aronreid/ups-to-esp32/docs/ups-adaptor-onepager.pdf

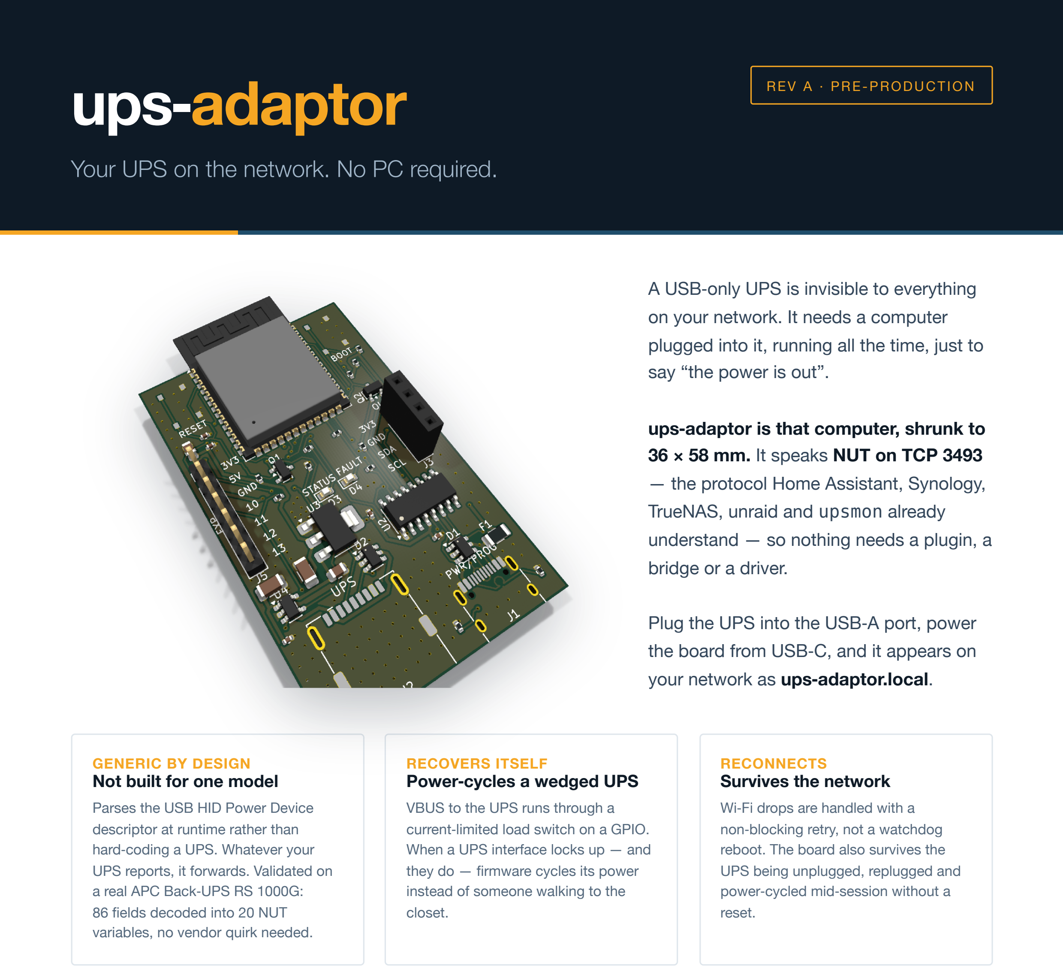
[picture p6: figure]
on your network. It needs a computer; say “the power is out”.; ups‑adaptor is that computer, shrunk to 36 × 58 mm. It speaks NUT on TCP 3493; TrueNAS, unraid and upsmon already; bridge or a driver.; Plug the UPS into the USB‑A port, power the board from USB‑C, and it appears on your network as ups‑adaptor.local.; GENERIC BY DESIGN Not built for one model; Parses the USB HID Power Device descriptor at runtime rather than hard‑coding a UPS. Whatever your UPS reports, it forwards. Validated on a real APC Back‑UPS RS 1000G: 86 fields decoded into 20 NUT variables, no vendor quirk needed.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

### A USB‑only UPS is invisible to everything

### plugged into it, running all the time, just to

— the protocol Home Assistant, Synology,

### understand — so nothing needs a plugin, a

## Technical specification

Controller | ESP32‑S3‑WROOM‑1‑N4 dual‑core Xtensa LX7, 4 MB flash
Wireless | Wi‑Fi 802.11 b/g/n, 2.4 GHz PCB antenna, Bluetooth disabled
UPS port | USB‑A host, USB 2.0 full speed 12 Mbps, HID Power Device class
VBUS to UPS | Switched, 1 A current limit fault flag to firmware, 100 µF bulk
Power & console | USB‑C: 5 V in, programming and serial on one connector
Protection | ESD array on both USB ports 2 A resettable polyfuse
Primary output | NUT server, TCP 3493 read‑only protocol subset
Secondary output | MQTT with Home Assistant discovery
Setup | Web UI over Wi‑Fi; SoftAP for first‑run provisioning
Discovery | mDNS — ups‑adaptor.local
Expansion | 4 × GPIO + 3V3 + 5V + GND I²C header for a 128×64 OLED
Board | 36 × 58 mm, 2 layer surface mount, case‑clip mounting

Open hardware & firmware. GPL‑3.0‑or‑later — KiCad sources, ESP‑IDF firmware and the test harness are all in the repository.

Rev A
Pre‑production. Not yet
fabricated.

Your UPS on the network. No PC required.
