aronreid/ups-to-esp32/firmware/components/ups_hid/ups_hid.c

/* SPDX-License-Identifier: GPL-3.0-or-later */
#include "ups_hid.h"
#include "hid_parser.h"
#include "tripplite_legacy.h"
#include "apc_modbus.h"
#include "status_hold.h"
#include "report_io.h"
#include "usb_guard.h"
#include "ups_vartab.h"
#include "ups_vars.h"
#include "ups_nutstatus.h"
#include "board.h"
#include "freertos/FreeRTOS.h"
#include "freertos/task.h"
#include "freertos/semphr.h"
#include "esp_log.h"
#include "esp_timer.h"
#include "esp_heap_caps.h"
#include "esp_attr.h"
#include "esp_system.h"
#include "usb/usb_host.h"
#include "usb/usb_helpers.h"
#include "mbedtls/sha256.h"
#include <math.h>
#include <string.h>

static const char *TAG = "ups_hid";

/* See usb_guard.h. RTC_NOINIT: survives the panic restart it exists to count. */
static RTC_NOINIT_ATTR usb_guard_state_t s_guard;
static usb_guard_level_t s_guard_level;
static int64_t s_live_until_us;

#define POLL_INTERVAL_MS      2000
#define FAILURES_BEFORE_RESET 5     /* ~10s of silence before a VBUS cycle */
/* After restoring VBUS, how long to wait for a bus-powered UPS to report that
 * it went away. A self-powered one never does; see do_recover(). */
#define VBUS_GONE_WAIT_MS     1500

/* How long to hold the last known status through an all-zero reading before
 * giving up and forcing a VBUS recovery. A CyberPower EC850LCD reported no
 * status bits for ~2 minutes after a test (2026-09-27, docs/rev-b.md); this
 * is comfortably longer than that observed glitch, short enough that a UPS
 * genuinely gone quiet still gets recovered well inside a shutdown script's
 * patience. */
#define STATUS_HOLD_US (5LL * 60 * 1000000)
_Static_assert(STATUS_HOLD_UNKNOWN == (uint32_t)UPS_STATUS_UNKNOWN,
               "status_hold.h's stand-in for UPS_STATUS_UNKNOWN drifted");

/* Recovery backoff. A UPS that is simply unplugged must not have its VBUS
 * cycled every ten seconds forever, but one that may yet come back must not be
 * abandoned either. Start at 10s and double to a 5 minute ceiling, reset on the
 * first good poll. */
#define RECOVERY_BACKOFF_MIN_US (10LL * 1000 * 1000)
#define RECOVERY_BACKOFF_MAX_US (300LL * 1000 * 1000)

static ups_data_t       s_data;
static hid_report_map_t s_map;
static SemaphoreHandle_t s_lock;

/* Kept outside ups_data_t because ups_hid_recover() resets that wholesale. */
static int64_t s_next_recovery_us;
static int64_t s_recovery_backoff_us = RECOVERY_BACKOFF_MIN_US;

/* A failed enumeration is tried again, on its own backoff. NEW_DEV fires once
 * per attach, so a UPS that fumbled its first descriptor read (a slow one, or
 * one still waking after a VBUS recovery) used to sit at "not detected" until
 * someone replugged it: the empty-port logic below kept the recovery idle,
 * because with nothing open there was nothing failing. */
#define ENUM_RETRY_MIN_US (2LL * 1000 * 1000)
#define ENUM_RETRY_MAX_US (60LL * 1000 * 1000)
static bool    s_enum_retry;            /* try s_dev_addr again at s_enum_retry_at_us */
static int64_t s_enum_retry_at_us;
static int64_t s_enum_backoff_us = ENUM_RETRY_MIN_US;
/* Enumeration failed and the device could not be closed (a control transfer
 * still parked): it counts as failing polls, so do_recover() takes over. */
static bool    s_enum_stuck;
/* The failure will not change on a retry: the address has gone, or the
 * device is not HID at all. */
static bool    s_enum_final;

static void ups_data_reset(ups_data_t *d)
{
    memset(d, 0, sizeof(*d));
    d->battery_charge    = UPS_VALUE_ABSENT;
    d->battery_runtime   = UPS_VALUE_ABSENT;
    d->battery_voltage   = UPS_VALUE_ABSENT;
    d->input_voltage     = UPS_VALUE_ABSENT;
    d->input_frequency   = UPS_VALUE_ABSENT;
    d->output_voltage    = UPS_VALUE_ABSENT;
    d->ups_load          = UPS_VALUE_ABSENT;
    d->ups_realpower     = UPS_VALUE_ABSENT;
    d->ups_realpower_nom = UPS_VALUE_ABSENT;
    d->ups_apparentpower = UPS_VALUE_ABSENT;
    d->status            = UPS_STATUS_UNKNOWN;
    d->battery_mfr_date[0] = '\0';
}

/* Values are read with GET_REPORT(Feature) on each poll. Feature, not Input:
 * a UPS keeps the authoritative reading there, and an Input report of the same
 * usage only arrives when the device chooses to send one.
 *           esp_hid's host component is input-report oriented and will not do
 *           this for us -- issue the control transfers directly (CLAUDE.md). */

/* ---- USB host plumbing ------------------------------------------------ */

#define USB_CLIENT_EVENT_TIMEOUT_MS 100
#define CTRL_TIMEOUT_MS             1000
/* NUT allows 6144. 2048 turned away real units: an Eaton (2053 bytes) and a
 * Legrand Keor DK 3K (2149) among the NUT issue captures, and three more sit
 * within 500 bytes of it. tools/test/test_nut_descriptors.py fails if any
 * capture outgrows this. */
#define REPORT_DESC_MAX             4096

#define USB_CLASS_HID               0x03
#define HID_DESC_TYPE               0x21
#define HID_REPORT_DESC_TYPE        0x22
#define REQ_GET_DESCRIPTOR          0x06
#define REQ_GET_REPORT              0x01
#define REQ_SET_REPORT              0x09
#define REPORT_TYPE_OUTPUT          0x02
#define REPORT_TYPE_FEATURE         0x03

static usb_host_client_handle_t s_client;
static usb_device_handle_t      s_dev;
static uint8_t                  s_dev_addr;
static bool                     s_dev_pending;
static uint8_t                  s_hid_iface = 0xFF;
static uint16_t                 s_report_desc_len;
static SemaphoreHandle_t        s_ctrl_done;
/* Legacy Tripp Lite (09ae:0001): a vendor protocol instead of HID Power
 * Device, answered on the interrupt IN endpoint. See tripplite_legacy.h. */
static bool                     s_legacy;
static uint8_t                  s_intr_ep;          /* 0 if the interface has none */
static uint16_t                 s_intr_mps;
static uint8_t                  s_intr_out_ep;      /* interrupt OUT, 0 if none */
/* APC Modbus over USB (apc_modbus.h): the descriptor carries the transport,
 * on these report IDs. The rest of its state is with NUT's variables. */
static bool                     s_mb;
static uint8_t                  s_mb_to, s_mb_from;
static SemaphoreHandle_t        s_intr_done;
static tl_config_t              s_tl;
static uint8_t                  s_report_desc[REPORT_DESC_MAX];

/* Worked out at enumeration; defined with the M1 polling code below. */
static void build_poll_plan(void);

/* The control table lives with the write path further down, but enumeration
 * and the poll plan both come first and need to see it. Kept in step with the
 * table by the static assert beside it. */
#define CTRL_COUNT 4
static const hid_field_t *s_ctrl_field[CTRL_COUNT];
static uint32_t discover_caps(void);

/* ManufacturerDate, Battery System 0x85. Neither a reading nor a control, so
 * it gets its own slot: read once per poll like everything else, but decoded
 * into text rather than a float. */
static const hid_field_t *s_date_field;

/* A command from another task, executed by the polling task. Declared here
 * because the poll loop and ups_hid_start are both above the definitions. */
typedef struct {
    ups_cmd_t cmd;
    int32_t   arg;
    /* Not a UPS command: a board-level VBUS power cycle, queued here so it
     * executes in ups_task like everything else that touches the report map. */
    bool      recover;
    /* Not a UPS command either: start (quiet_on) or end a quiet spell, see
     * ups_hid_quiet(). */
    bool      quiet;
    bool      quiet_on;
} cmd_req_t;
static QueueHandle_t s_cmd_q;
static QueueHandle_t s_cmd_done;
/* No USB traffic to the UPS: no interrupt pipe, no polls, no enumeration, no
 * commands. Set and cleared only in ups_task, by ups_hid_quiet(). */
static bool s_quiet;
static esp_err_t execute_cmd(const cmd_req_t *r);
static esp_err_t do_recover(void);
static void bind_vars(uint16_t vid, uint16_t pid);   /* NUT's tables, below */

static void ctrl_cb(usb_transfer_t *xfer)
{
    xSemaphoreGive((SemaphoreHandle_t)xfer->context);
}

/* A control transfer that timed out, still owned by the USB stack.
 *
 * THIS IS WHY BOARDS ON A CYBERPOWER CRASHED. ctrl_in and ctrl_out used to
 * free a transfer that had not completed in CTRL_TIMEOUT_MS -- while it was
 * still queued on the control pipe. The pipe's queue then pointed into freed
 * memory, the next allocation (a TLS handshake is the big one: an update
 * check) wrote over it, and when the stack next flushed the control pipe it
 * walked a corrupted list inside its critical section until the interrupt
 * watchdog reset the board. Recorded on a CyberPower EC850LCD, twice, v0.09:
 * hcd_pipe_command -> _pipe_cmd_flush -> _buffer_flush_all, from
 * usbh_process's handle_ep0_flush. An APC, which always answers in time,
 * never hit it.
 *
 * ESP-IDF has no public way to cancel a control transfer, and closing a
 * device with one in flight trips an assert. So a late one is PARKED: no new
 * control transfer is submitted until it completes -- when the UPS answers,
 * or the device goes away -- and only then is it freed. Only one control
 * transfer is ever in flight, so the shared completion semaphore stays
 * unambiguous. */
static usb_transfer_t *s_ctrl_parked;

/* Reclaim the parked transfer if it has completed, waiting up to wait_ms.
 * True when nothing is parked any more. */
static bool ctrl_reclaim(int wait_ms)
{
    if (!s_ctrl_parked) return true;
    for (int waited = 0; ; waited += 10) {
        if (xSemaphoreTake(s_ctrl_done, 0) == pdTRUE) {
            ESP_LOGW(TAG, "late control transfer completed (status %d); freed",
                     s_ctrl_parked->status);
            usb_host_transfer_free(s_ctrl_parked);
            s_ctrl_parked = NULL;
            return true;
        }
        if (waited >= wait_ms) return false;
        usb_host_client_handle_events(s_client, pdMS_TO_TICKS(10));
    }
}

/* Submit a control transfer and wait for it. False on refusal or timeout; a
 * timed-out transfer is parked, never freed -- see s_ctrl_parked. */
static bool ctrl_run(usb_transfer_t *xfer)
{
    xSemaphoreTake(s_ctrl_done, 0);         /* nothing else is in flight */
    if (usb_host_transfer_submit_control(s_client, xfer) != ESP_OK) return false;
    /* Transfer callbacks are delivered from usb_host_client_handle_events,
     * which this same task owns. Blocking on the semaphore without pumping
     * events deadlocks: the callback that would give it can never run. So
     * pump while waiting. */
    for (int waited = 0; waited < CTRL_TIMEOUT_MS; waited += 10) {
        usb_host_client_handle_events(s_client, pdMS_TO_TICKS(10));
        if (xSemaphoreTake(s_ctrl_done, 0) == pdTRUE) return true;
    }
    ESP_LOGW(TAG, "control transfer timed out; parked until the UPS answers");
    s_ctrl_parked = xfer;
    return false;
}

/* Close the device -- but never with a control transfer in flight, which
 * ESP-IDF asserts on. True if it was closed. */
static bool ipipe_stop(void);

static bool dev_close_safely(void)
{
    /* The standing interrupt transfer first: releasing the interface with it
     * still submitted is refused, and freeing it under the stack is how this
     * driver corrupted the heap once before. */
    if (!ipipe_stop()) {
        ESP_LOGE(TAG, "the interrupt transfer will not cancel; not closing the device yet");
        return false;
    }
    if (!ctrl_reclaim(1000)) {
        ESP_LOGE(TAG, "a control transfer is still in flight; not closing the device yet");
        return false;
    }
    usb_host_interface_release(s_client, s_dev, s_hid_iface);
    usb_host_device_close(s_client, s_dev);
    return true;
}

/* Blocking control OUT transfer: same shape as ctrl_in, with the payload
 * copied in after the setup packet instead of read out of it. Returns true if
 * the device ACKed. */
static bool ctrl_out(uint8_t bmRequestType, uint8_t bRequest, uint16_t wValue,
                     uint16_t wIndex, const uint8_t *data, uint16_t len)
{
    if (!ctrl_reclaim(2000)) return false;  /* the control pipe is still busy */
    usb_transfer_t *xfer = NULL;
    if (usb_host_transfer_alloc(sizeof(usb_setup_packet_t) + len, 0, &xfer) != ESP_OK) {
        return false;
    }

    usb_setup_packet_t *setup = (usb_setup_packet_t *)xfer->data_buffer;
    setup->bmRequestType = bmRequestType;
    setup->bRequest      = bRequest;
    setup->wValue        = wValue;
    setup->wIndex        = wIndex;
    setup->wLength       = len;
    if (len) memcpy(xfer->data_buffer + sizeof(usb_setup_packet_t), data, len);

    xfer->device_handle    = s_dev;
    xfer->bEndpointAddress = 0;
    xfer->num_bytes        = sizeof(usb_setup_packet_t) + len;
    xfer->callback         = ctrl_cb;
    xfer->context          = s_ctrl_done;

    if (!ctrl_run(xfer)) {
        if (xfer != s_ctrl_parked) usb_host_transfer_free(xfer);   /* refused */
        return false;
    }
    bool ok = xfer->status == USB_TRANSFER_STATUS_COMPLETED;
    usb_host_transfer_free(xfer);
    return ok;
}

/* Blocking control IN transfer. Returns bytes of payload, or -1. */
/* The attached device's EP0 max packet size, from its device descriptor. 64
 * until one is known: a multiple of every legal EP0 size, so rounding to it is
 * never too small. */
static uint8_t s_ep0_mps = 64;

/* The data stage of a control IN is sized in whole packets, not to wLength.
 * The host controller writes whatever packet the device sends, and some UPSes
 * answer a GET_REPORT with a full packet longer than the report asked for (an
 * APC Back-UPS ES 600M1 does, on its first feature poll). With the buffer cut
 * to exactly wLength, ESP-IDF's HCD does not fail the transfer: it asserts
 * (hcd_dwc.c, _buffer_parse_ctrl), and the board reboots and does it again on
 * every boot, off the network, until the UPS is unplugged. ESP-IDF documents
 * usb_round_up_to_mps() for exactly this; intr_in() already did it. */
static int ctrl_in(uint8_t bmRequestType, uint8_t bRequest, uint16_t wValue,
                   uint16_t wIndex, uint16_t wLength, uint8_t *out)
{
    if (!ctrl_reclaim(2000)) return -1;     /* the control pipe is still busy */
    size_t data = usb_round_up_to_mps(wLength, s_ep0_mps);
    usb_transfer_t *xfer = NULL;
    if (usb_host_transfer_alloc(sizeof(usb_setup_packet_t) + data, 0, &xfer) != ESP_OK) {
        return -1;
    }

    usb_setup_packet_t *setup = (usb_setup_packet_t *)xfer->data_buffer;
    setup->bmRequestType = bmRequestType;
    setup->bRequest      = bRequest;
    setup->wValue        = wValue;
    setup->wIndex        = wIndex;
    setup->wLength       = wLength;

    xfer->device_handle    = s_dev;
    xfer->bEndpointAddress = 0;
    xfer->num_bytes        = sizeof(usb_setup_packet_t) + data;
    xfer->callback         = ctrl_cb;
    xfer->context          = s_ctrl_done;

    int got = -1;
    if (!ctrl_run(xfer)) {
        if (xfer != s_ctrl_parked) usb_host_transfer_free(xfer);   /* refused */
        return -1;
    }
    if (xfer->status == USB_TRANSFER_STATUS_COMPLETED) {
        got = xfer->actual_num_bytes - sizeof(usb_setup_packet_t);
        if (got < 0) got = 0;
        if (got > wLength) got = wLength;
        if (out && got > 0) memcpy(out, xfer->data_buffer + sizeof(usb_setup_packet_t), got);
    }
    usb_host_transfer_free(xfer);
    return got;
}

/* Set by client_event_cb, acted on by ups_task at a point where no control
 * transfer is in flight. See the DEV_GONE case for why the teardown cannot
 * happen in the callback. */
static volatile bool s_dev_gone;

static void client_event_cb(const usb_host_client_event_msg_t *msg, void *arg)
{
    switch (msg->event) {
    case USB_HOST_CLIENT_EVENT_NEW_DEV:
        s_dev_addr = msg->new_dev.address;
        s_dev_pending = true;
        s_enum_retry = false;               /* a fresh attach starts afresh */
        s_enum_backoff_us = ENUM_RETRY_MIN_US;
        /* A crash from here until USB_GUARD_LIVE_US passes is charged to it. */
        s_guard.live = 1;
        s_live_until_us = esp_timer_get_time() + USB_GUARD_LIVE_US;
        ESP_LOGI(TAG, "USB device attached at address %u", s_dev_addr);
        break;
    case USB_HOST_CLIENT_EVENT_DEV_GONE:
        /* Heap is logged on every attach and detach so a leak across
         * plug cycles is VISIBLE. Repeated enumeration is where USB stacks
         * leak handles, and it will not show up as a failure for hundreds of
         * cycles -- by which time it is a field fault, not a bench one.
         * CLAUDE.md requires this board to survive replugging indefinitely. */
        ESP_LOGW(TAG, "USB device disconnected (heap %u free, %u low-water)",
                 (unsigned)esp_get_free_heap_size(),
                 (unsigned)esp_get_minimum_free_heap_size());
        /* FLAG ONLY. Do not release the interface or close the device here.
         *
         * This callback is dispatched by usb_host_client_handle_events(), and
         * ctrl_in()/ctrl_out() have to CALL that while waiting for a control
         * transfer to complete -- this task owns the event pump, so blocking
         * without pumping would deadlock. The consequence is that a device
         * disconnecting mid-poll runs this callback from INSIDE the transfer
         * wait, and the old code then released the interface and closed the
         * device handle while that transfer was still submitted against it,
         * after which ctrl_in() freed the transfer the stack still owned.
         *
         * Unplugging a UPS during a poll is not an exotic case; it is the
         * documented requirement in CLAUDE.md that this board survive being
         * unplugged mid-session. The attach path already had this right --
         * USB_HOST_CLIENT_EVENT_NEW_DEV only sets s_dev_pending and lets
         * ups_task open the device at a safe point. Detach now matches. */
        s_dev_gone = true;
        break;
    default:
        break;
    }
}

/* A UPS that has stopped answering must stop reporting numbers.
 *
 * An unplug clears everything through ups_data_reset(), but a UPS that is
 * still enumerated and has simply gone deaf -- the exact failure the VBUS
 * recovery exists for -- took a different path: `attached` went false and the
 * last good readings stayed behind it. The web UI then showed "UPS not
 * detected" next to a 100% battery and 120 V input, and NUT would have served
 * the same numbers to a client deciding whether to shut a NAS down.
 *
 * Identity is deliberately kept. Knowing WHICH UPS stopped answering is useful
 * and cannot be stale in any way that matters; a voltage can. */
static void invalidate_readings(ups_data_t *d)
{
    d->battery_charge    = UPS_VALUE_ABSENT;
    d->battery_runtime   = UPS_VALUE_ABSENT;
    d->battery_voltage   = UPS_VALUE_ABSENT;
    d->input_voltage     = UPS_VALUE_ABSENT;
    d->input_frequency   = UPS_VALUE_ABSENT;
    d->output_voltage    = UPS_VALUE_ABSENT;
    d->ups_load          = UPS_VALUE_ABSENT;
    d->ups_realpower     = UPS_VALUE_ABSENT;
    d->ups_realpower_nom = UPS_VALUE_ABSENT;
    d->ups_apparentpower = UPS_VALUE_ABSENT;
    d->status            = UPS_STATUS_UNKNOWN;
}

static void usb_lib_task(void *arg)
{
    for (;;) {
        uint32_t flags;
        usb_host_lib_handle_events(portMAX_DELAY, &flags);
        if (flags & USB_HOST_LIB_EVENT_FLAGS_NO_CLIENTS) {
            usb_host_device_free_all();
        }
    }
}

/* Walk the configuration descriptor for a HID interface and its report
 * descriptor length. Generic: matches on class, never on VID/PID. */
/* Every HID interface on the device, in order. A composite device can have
 * several, and the UPS is not always the first: a Liebert PSI5 (10af:0002)
 * puts a 27-byte vendor tunnel on interface 0 and the UPS on 1; NUT's Arduino
 * and Powervar subdrivers name interfaces 2 and 1. choose_hid_interface()
 * picks by content, not by a table of numbers. */
#define MAX_HID_IFACES 4
static struct { uint8_t iface; uint16_t desc_len; uint8_t ep; uint16_t mps; uint8_t ep_out; } s_hid_cand[MAX_HID_IFACES];
static size_t s_hid_cand_n;

static bool find_hid_interface(const usb_config_desc_t *cfg)
{
    int offset = 0;
    const usb_standard_desc_t *d = (const usb_standard_desc_t *)cfg;
    int cur = -1;                           /* index in s_hid_cand, or -1 */

    s_hid_cand_n = 0;
    while ((d = usb_parse_next_descriptor(d, cfg->wTotalLength, &offset)) != NULL) {
        if (d->bDescriptorType == USB_B_DESCRIPTOR_TYPE_INTERFACE) {
            const usb_intf_desc_t *i = (const usb_intf_desc_t *)d;
            cur = -1;
            if (i->bInterfaceClass == USB_CLASS_HID && i->bAlternateSetting == 0 &&
                s_hid_cand_n < MAX_HID_IFACES) {
                cur = (int)s_hid_cand_n;
                s_hid_cand[cur].iface = i->bInterfaceNumber;
                s_hid_cand[cur].desc_len = 0;
                s_hid_cand[cur].ep = 0;
                s_hid_cand[cur].mps = 0;
                s_hid_cand[cur].ep_out = 0;
            }
        } else if (cur >= 0 && d->bDescriptorType == HID_DESC_TYPE) {
            /* HID descriptor: wDescriptorLength is at offset 7. */
            const uint8_t *raw = (const uint8_t *)d;
            if (d->bLength >= 9 && !s_hid_cand[cur].desc_len) {
                s_hid_cand[cur].desc_len = (uint16_t)(raw[7] | (raw[8] << 8));
                if ((size_t)cur == s_hid_cand_n) s_hid_cand_n++;
            }
        } else if (cur >= 0 && d->bDescriptorType == USB_B_DESCRIPTOR_TYPE_ENDPOINT) {
            /* The endpoint descriptors follow the HID descriptor. The IN
             * endpoint carries the interrupt pipe and the legacy Tripp Lite
             * replies; the OUT one, APC Modbus requests (apc_modbus.h). */
            const usb_ep_desc_t *ep = (const usb_ep_desc_t *)d;
            if ((ep->bEndpointAddress & 0x80) && (ep->bmAttributes & 0x03) == 0x03 &&
                !s_hid_cand[cur].ep) {
                s_hid_cand[cur].ep = ep->bEndpointAddress;
                s_hid_cand[cur].mps = ep->wMaxPacketSize & 0x7FF;
            } else if (!(ep->bEndpointAddress & 0x80) && (ep->bmAttributes & 0x03) == 0x03 &&
                       !s_hid_cand[cur].ep_out) {
                s_hid_cand[cur].ep_out = ep->bEndpointAddress;
            }
        }
    }
    if (!s_hid_cand_n) return false;
    s_hid_iface = s_hid_cand[0].iface;      /* the default: the first */
    s_report_desc_len = s_hid_cand[0].desc_len;
    s_intr_ep = s_hid_cand[0].ep;
    s_intr_mps = s_hid_cand[0].mps;
    s_intr_out_ep = s_hid_cand[0].ep_out;
    return true;
}

static int ctrl_in(uint8_t bmRequestType, uint8_t bRequest, uint16_t wValue,
                   uint16_t wIndex, uint16_t wLength, uint8_t *out);

/* With more than one HID interface, the first whose report descriptor is a
 * UPS's (hid_is_power_device()). None is: keep the first, as before. */
static void choose_hid_interface(void)
{
    if (s_hid_cand_n < 2) return;
    for (size_t k = 0; k < s_hid_cand_n; k++) {
        uint16_t len = s_hid_cand[k].desc_len;
        if (!len || len > REPORT_DESC_MAX) continue;
        int n = ctrl_in(0x81, REQ_GET_DESCRIPTOR, (uint16_t)(HID_REPORT_DESC_TYPE << 8),
                        s_hid_cand[k].iface, len, s_report_desc);
        if (n > 0 && hid_is_power_device(s_report_desc, (size_t)n)) {
            s_hid_iface = s_hid_cand[k].iface;
            s_report_desc_len = s_hid_cand[k].desc_len;
            s_intr_ep = s_hid_cand[k].ep;
            s_intr_mps = s_hid_cand[k].mps;
            s_intr_out_ep = s_hid_cand[k].ep_out;
            ESP_LOGI(TAG, "%u HID interfaces; the UPS is interface %u",
                     (unsigned)s_hid_cand_n, s_hid_iface);
            return;
        }
    }
    ESP_LOGW(TAG, "%u HID interfaces, none a UPS descriptor; using interface %u",
             (unsigned)s_hid_cand_n, s_hid_iface);
}

/* Blocking interrupt IN read. Returns bytes read, or -1 on timeout or error.
 *
 * A timed-out transfer is still owned by the USB stack. It is CANCELLED --
 * halt, flush, clear -- and its completion awaited before it is freed; freeing
 * a transfer the stack still holds is how this driver once corrupted the heap
 * on unplug. */
static int intr_in(uint8_t *out, size_t cap, int timeout_ms)
{
    if (!s_intr_ep) return -1;
    size_t mps = s_intr_mps ? s_intr_mps : TL_PKT;
    /* Whole packets, and only as many as one TL_PKT reply needs. ESP-IDF ends
     * an interrupt IN transfer on a short packet or a full buffer, nothing
     * else: asking for 64 bytes on an 8-byte endpoint left every exact 8-byte
     * reply waiting for seven more, so each query timed out and the UPS was
     * never found. */
    size_t want = mps;
    while (want < TL_PKT) want += mps;
    if (want > cap) return -1;

    usb_transfer_t *xfer = NULL;
    if (usb_host_transfer_alloc(want, 0, &xfer) != ESP_OK) return -1;
    xfer->device_handle    = s_dev;
    xfer->bEndpointAddress = s_intr_ep;
    xfer->num_bytes        = want;
    xfer->callback         = ctrl_cb;
    xfer->context          = s_intr_done;
    xSemaphoreTake(s_intr_done, 0);         /* drop any stale completion */

    if (usb_host_transfer_submit(xfer) != ESP_OK) {
        usb_host_transfer_free(xfer);
        return -1;
    }
    bool done = false;
    for (int waited = 0; waited < timeout_ms; waited += 10) {
        usb_host_client_handle_events(s_client, pdMS_TO_TICKS(10));
        if (xSemaphoreTake(s_intr_done, 0) == pdTRUE) { done = true; break; }
    }
    if (!done) {
        usb_host_endpoint_halt(s_dev, s_intr_ep);
        usb_host_endpoint_flush(s_dev, s_intr_ep);
        for (int waited = 0; waited < 500 && !done; waited += 10) {
            usb_host_client_handle_events(s_client, pdMS_TO_TICKS(10));
            done = xSemaphoreTake(s_intr_done, 0) == pdTRUE;
        }
        usb_host_endpoint_clear(s_dev, s_intr_ep);
        if (!done) {
            /* Never completed even when cancelled: leak it rather than free
             * memory the stack may still write to. */
            ESP_LOGE(TAG, "interrupt transfer would not cancel; leaking %u bytes",
                     (unsigned)want);
            return -1;
        }
        usb_host_transfer_free(xfer);
        return -1;
    }
    int got = -1;
    if (xfer->status == USB_TRANSFER_STATUS_COMPLETED) {
        got = xfer->actual_num_bytes;
        if (got > (int)cap) got = (int)cap;
        memcpy(out, xfer->data_buffer, got);
    }
    usb_host_transfer_free(xfer);
    return got;
}

/* ---- The interrupt pipe ------------------------------------------------
 *
 * A UPS also sends Input reports on its interrupt endpoint when something
 * changes. NUT maps them by path onto the same variables and status tokens
 * as the polled Feature reports, so a change shows up before the next poll.
 * One transfer stands submitted; its callback only copies the bytes and sets
 * a flag, and ups_task does the rest and resubmits at a safe point. Stopping
 * it (dev_close_safely, every way a device is closed) cancels it, waits for
 * its completion, and only then frees it -- or refuses to close.
 *
 * Not used for the legacy Tripp Lite protocol (it talks on this endpoint
 * itself), nor while usb_guard.h has stopped polling. */
static usb_transfer_t  *s_ipipe;
static volatile bool    s_ipipe_busy, s_ipipe_ready;
static uint8_t          s_ipipe_buf[64];
static volatile int     s_ipipe_len;
static bool             s_ipipe_on;

static void ipipe_cb(usb_transfer_t *x)
{
    if (x->status == USB_TRANSFER_STATUS_COMPLETED && x->actual_num_bytes > 0) {
        int n = x->actual_num_bytes;
        if (n > (int)sizeof(s_ipipe_buf)) n = sizeof(s_ipipe_buf);
        memcpy(s_ipipe_buf, x->data_buffer, n);
        s_ipipe_len = n;
        s_ipipe_ready = true;
    }
    s_ipipe_busy = false;
}

static void ipipe_start(void)
{
    s_ipipe_on = false;
    if (!s_intr_ep || s_legacy || s_guard_level != USB_GUARD_NORMAL || s_ipipe || s_quiet) return;
    size_t mps = s_intr_mps ? s_intr_mps : 8;
    size_t want = mps;                      /* whole packets, at least 64 bytes */
    while (want < sizeof(s_ipipe_buf)) want += mps;
    if (usb_host_transfer_alloc(want, 0, &s_ipipe) != ESP_OK) { s_ipipe = NULL; return; }
    s_ipipe->device_handle    = s_dev;
    s_ipipe->bEndpointAddress = s_intr_ep;
    s_ipipe->num_bytes        = want;
    s_ipipe->callback         = ipipe_cb;
    s_ipipe->context          = NULL;
    s_ipipe_busy = s_ipipe_ready = false;
    s_ipipe_on = true;
    ESP_LOGI(TAG, "listening on interrupt endpoint 0x%02x", s_intr_ep);
}

static void ipipe_kick(void)
{
    if (!s_ipipe_on || s_ipipe_busy || s_dev_gone || !s_dev || s_quiet) return;
    s_ipipe_busy = true;
    if (usb_host_transfer_submit(s_ipipe) != ESP_OK) {
        s_ipipe_busy = false;
        s_ipipe_on = false;                 /* polling carries on regardless */
        ESP_LOGW(TAG, "interrupt endpoint refused a transfer; not listening");
    }
}

static bool ipipe_stop(void)
{
    s_ipipe_on = false;
    if (!s_ipipe) return true;
    if (s_ipipe_busy && s_dev) {
        usb_host_endpoint_halt(s_dev, s_intr_ep);
        usb_host_endpoint_flush(s_dev, s_intr_ep);
        for (int w = 0; w < 500 && s_ipipe_busy; w += 10) {
            usb_host_client_handle_events(s_client, pdMS_TO_TICKS(10));
        }
        usb_host_endpoint_clear(s_dev, s_intr_ep);
        if (s_ipipe_busy) return false;     /* still the stack's: do not free */
    }
    usb_host_transfer_free(s_ipipe);
    s_ipipe = NULL;
    s_ipipe_ready = false;
    return true;
}

/* Start or end a quiet spell. ups_task only: see ups_hid_quiet(). Quiet takes
 * effect at once for anything not yet sent; the interrupt pipe's standing
 * transfer is cancelled here, while nothing else is touching flash. */
static esp_err_t set_quiet(bool on)
{
    s_quiet = on;
    if (on) {
        ESP_LOGI(TAG, "quiet: UPS USB traffic paused");
        return ipipe_stop() ? ESP_OK : ESP_ERR_TIMEOUT;
    }
    ESP_LOGI(TAG, "quiet over: UPS USB traffic resumed");
    if (s_ipipe) s_ipipe_on = true;         /* a cancel that never came back */
    else if (s_dev && !s_dev_gone && s_guard_level == USB_GUARD_NORMAL) ipipe_start();
    return ESP_OK;
}

/* One legacy command and its reply. The UPS answers on the interrupt endpoint
 * a moment later, and echoes its PREVIOUS reply if it did not take this
 * command, so a reply counts only if it starts with this command's letter.
 *
 * Bounded well below NUT's loop, which can block for 100 s: this runs in
 * ups_task, and a stuck poll holds up the command queue and the recovery
 * logic behind it. Three sends, each read up to three times. */
static bool tl_xfer(const char *msg, size_t len, uint8_t reply[TL_PKT])
{
    uint8_t pkt[TL_PKT];
    tl_build_cmd((const uint8_t *)msg, len, pkt);
    for (int send = 0; send < 3; send++) {
        if (!ctrl_out(0x21, REQ_SET_REPORT, (uint16_t)(REPORT_TYPE_FEATURE << 8),
                      s_hid_iface, pkt, TL_PKT)) {
            continue;
        }
        vTaskDelay(pdMS_TO_TICKS(100));     /* NUT: replies take 80-90 ms */
        for (int rx = 0; rx < 3; rx++) {
            uint8_t buf[64];
            int n = intr_in(buf, sizeof(buf), 400);
            if (n >= TL_PKT && tl_reply_is_for(pkt, buf)) {
                memcpy(reply, buf, TL_PKT);
                return true;
            }
        }
    }
    return false;
}

/* Legacy enumeration: which protocol, watchdog off, configuration. */
static bool tl_enumerate(ups_data_t *local)
{
    if (!s_intr_ep) {
        ESP_LOGE(TAG, "legacy Tripp Lite without an interrupt IN endpoint");
        return false;
    }
    if (!s_intr_done) s_intr_done = xSemaphoreCreateBinary();
    if (!s_intr_done) return false;

    uint8_t r[TL_PKT];
    if (!tl_xfer("\0", 2, r)) {
        ESP_LOGE(TAG, "legacy Tripp Lite: no answer to the protocol query");
        return false;
    }
    uint16_t proto = tl_protocol_from_reply(r);
    tl_config_init(&s_tl, tl_decode_protocol(proto));
    ESP_LOGI(TAG, "legacy Tripp Lite, protocol %04x: %s", proto, tl_model_name(s_tl.model));

    /* The watchdog powers the load off if nothing talks to the UPS in time.
     * NUT turns it off on every model but SMARTPRO, which has none. */
    if (s_tl.model != TL_SMARTPRO && !tl_xfer("W\0", 3, r)) {
        ESP_LOGW(TAG, "legacy Tripp Lite: could not turn the watchdog off");
    }
    if (tl_xfer("V", 2, r)) tl_decode_v(&s_tl, r);
    ESP_LOGI(TAG, "legacy Tripp Lite: %d V input, %d V battery",
             s_tl.input_nominal, s_tl.battery_nominal);

    if (!local->mfr[0]) strlcpy(local->mfr, "Tripp Lite", sizeof(local->mfr));
    local->caps = 0;        /* no controls ported: tests and shutdown stay NUT-only */
    s_legacy = true;
    return true;
}

/* One legacy poll into d. False only when the UPS stops answering; an
 * unrecognised status code keeps the readings and reports the status as
 * unknown, rather than counting as a failure -- which would send a unit that
 * always says it into the VBUS recovery loop. */
static bool tl_poll(ups_data_t *d)
{
    char cmds[4];
    size_t n = tl_poll_commands(s_tl.model, cmds);
    tl_reading_t rd;
    tl_reading_init(&rd);
    for (size_t i = 0; i < n; i++) {
        char msg[2] = { cmds[i], 0 };
        uint8_t r[TL_PKT];
        if (!tl_xfer(msg, 2, r)) return false;
        switch (cmds[i]) {
        case 'S': tl_decode_s(&s_tl, r, &rd); break;
        case 'B': tl_decode_b(&s_tl, r, &rd); break;
        case 'D': tl_decode_d(&s_tl, r, &rd); break;
        case 'T': tl_decode_t(&s_tl, r, &rd); break;
        case 'L': tl_decode_l(&s_tl, r, &rd); break;
        default: break;
        }
    }
    tl_estimate_charge(&rd);

    uint32_t st = 0;
    if (rd.status & TL_ST_OL)   st |= UPS_STATUS_ONLINE;
    if (rd.status & TL_ST_OB)   st |= UPS_STATUS_ONBATT | UPS_STATUS_DISCHARGE;
    if (rd.status & TL_ST_LB)   st |= UPS_STATUS_LOWBATT;
    if (rd.status & TL_ST_RB)   st |= UPS_STATUS_REPLACEBATT;
    if (rd.status & TL_ST_OVER) st |= UPS_STATUS_OVERLOAD;
    d->status = rd.stale ? UPS_STATUS_UNKNOWN : st;

    d->battery_charge  = rd.battery_charge;
    d->battery_voltage = rd.battery_voltage;
    d->input_voltage   = rd.input_voltage;
    d->input_frequency = rd.input_frequency;
    d->output_voltage  = rd.output_voltage;
    d->ups_load        = rd.load;
    return true;
}

static void read_string(uint8_t index, char *out, size_t cap)
{
    out[0] = '\0';
    if (!index) return;
    uint8_t buf[128];
    /* 0x0409 = US English. */
    int n = ctrl_in(0x80, REQ_GET_DESCRIPTOR, (uint16_t)(0x0300 | index), 0x0409,
                    sizeof(buf), buf);
    if (n < 2) return;

    /* bLength is authoritative, NOT the transfer length. We asked for 128
     * bytes; what comes back past the descriptor's own length is padding or
     * whatever was in the buffer, and decoding it produced "EC850LCD???" from
     * a CyberPower EC850LCD -- three characters of junk that then travelled
     * out through NUT's ups.model to every client. */
    size_t len = buf[0];
    if (len > (size_t)n) len = (size_t)n;

    size_t o = 0;
    for (size_t i = 2; i + 1 < len && o + 1 < cap; i += 2) {
        uint16_t ch = buf[i] | (buf[i + 1] << 8);
        /* Anything outside printable ASCII is DROPPED rather than replaced
         * with '?'. These strings end up in ups.model and on the status page,
         * where a client shows them verbatim, so a shorter honest string beats
         * a padded one. Non-Latin names are the cost, and no UPS ships one. */
        if (ch >= 0x20 && ch < 0x7F) out[o++] = (char)ch;
    }
    out[o] = '\0';
    while (o && out[o - 1] == ' ') out[--o] = '\0';   /* APC pads with spaces */
}

/* Open the attached device, claim its HID interface, fetch and parse the
 * report descriptor. Returns true when the device is ready to poll. */
static bool enumerate(void)
{
    s_enum_final = false;
    esp_err_t oerr = usb_host_device_open(s_client, s_dev_addr, &s_dev);
    if (oerr != ESP_OK) {
        ESP_LOGE(TAG, "device_open failed: %s", esp_err_to_name(oerr));
        s_dev = NULL;
        s_enum_final = (oerr == ESP_ERR_NOT_FOUND);     /* it has gone */
        return false;
    }

    const usb_device_desc_t *dd = NULL;
    if (usb_host_get_device_descriptor(s_dev, &dd) != ESP_OK) {
        ESP_LOGE(TAG, "get_device_desc failed");
        return false;
    }
    s_ep0_mps = dd->bMaxPacketSize0 ? dd->bMaxPacketSize0 : 64;

    const usb_config_desc_t *cfg = NULL;
    if (usb_host_get_active_config_descriptor(s_dev, &cfg) != ESP_OK) {
        ESP_LOGE(TAG, "get_config_desc failed");
        return false;
    }

    if (!find_hid_interface(cfg)) {
        ESP_LOGE(TAG, "no HID interface on %04x:%04x -- not a HID Power Device?",
                 dd->idVendor, dd->idProduct);
        s_enum_final = true;
        return false;
    }

    choose_hid_interface();
    if (usb_host_interface_claim(s_client, s_dev, s_hid_iface, 0) != ESP_OK) {
        ESP_LOGE(TAG, "interface_claim(%u) failed", s_hid_iface);
        return false;
    }

    ups_data_t local;
    ups_data_reset(&local);
    local.vid = dd->idVendor;
    local.pid = dd->idProduct;
    read_string(dd->iManufacturer, local.mfr, sizeof(local.mfr));
    read_string(dd->iProduct, local.model, sizeof(local.model));
    read_string(dd->iSerialNumber, local.serial, sizeof(local.serial));

    ESP_LOGI(TAG, "%04x:%04x  %s %s  serial %s",
             local.vid, local.pid, local.mfr, local.model, local.serial);
    ESP_LOGI(TAG, "heap %u free, %u low-water",
             (unsigned)esp_get_free_heap_size(),
             (unsigned)esp_get_minimum_free_heap_size());
    ESP_LOGI(TAG, "HID interface %u, report descriptor %u bytes",
             s_hid_iface, s_report_desc_len);

    s_legacy = false;
    if (local.vid == TL_VID && local.pid == TL_LEGACY_PID) {
        if (!tl_enumerate(&local)) return false;
        local.attached = true;
        local.last_update_us = esp_timer_get_time();
        xSemaphoreTake(s_lock, portMAX_DELAY);
        s_data = local;
        xSemaphoreGive(s_lock);
        return true;
    }

    uint16_t want = s_report_desc_len;
    if (want > REPORT_DESC_MAX) {
        ESP_LOGE(TAG, "report descriptor %u bytes exceeds buffer %d",
                 want, REPORT_DESC_MAX);
        return false;
    }

    /* GET_DESCRIPTOR(Report) on the interface. */
    int n = ctrl_in(0x81, REQ_GET_DESCRIPTOR,
                    (uint16_t)(HID_REPORT_DESC_TYPE << 8), s_hid_iface,
                    want, s_report_desc);
    /* Shorter than the HID descriptor promised is a UPS's own mistake, and
     * NUT warns and parses what came. Refusing it lost the UPS outright. */
    if (n <= 0) {
        ESP_LOGE(TAG, "report descriptor read returned %d, wanted %u", n, want);
        return false;
    }
    if (n < (int)want) {
        ESP_LOGW(TAG, "report descriptor is %d bytes, not the %u promised; using it",
                 n, want);
        s_report_desc_len = (uint16_t)n;
    }

    /* Its fingerprint, for the fleet's table of UPS models seen. */
    uint8_t sum[32];
    if (mbedtls_sha256(s_report_desc, n, sum, 0) == 0) {
        for (int i = 0; i < 8; i++) snprintf(local.desc_hash + 2 * i, 3, "%02x", sum[i]);
    }
    local.desc_len = (uint16_t)n;

    /* Dump it so it can be diffed byte-for-byte against a host capture. */
    ESP_LOGI(TAG, "---- BEGIN REPORT DESCRIPTOR (%d bytes) ----", n);
    for (int i = 0; i < n; i += 16) {
        char line[64];
        int o = 0;
        for (int j = i; j < i + 16 && j < n; j++) {
            o += snprintf(line + o, sizeof(line) - o, "%02x", s_report_desc[j]);
        }
        ESP_LOGI(TAG, "%s", line);
    }
    ESP_LOGI(TAG, "---- END REPORT DESCRIPTOR ----");

    hid_parse_report_descriptor(s_report_desc, n, &s_map);
    hid_apply_quirks(&s_map, local.vid, local.pid);
    /* Caps first: build_poll_plan() adds the control reports to the polling
     * set, and it can only do that once discover_caps() has resolved them.
     * The other way round the controls are found but never read back, so the
     * page shows a beeper state of zero for a UPS that answers perfectly. */
    local.caps = discover_caps();
    build_poll_plan();
    bind_vars(local.vid, local.pid);
    s_mb = apcmb_find_reports(s_report_desc, n, &s_mb_to, &s_mb_from);
    if (s_mb) {
        ESP_LOGI(TAG, "APC Modbus reports 0x%02x/0x%02x; requests by %s", s_mb_to, s_mb_from,
                 s_intr_out_ep ? "interrupt OUT" : "SET_REPORT");
    }

    local.attached = true;
    local.last_update_us = esp_timer_get_time();

    xSemaphoreTake(s_lock, portMAX_DELAY);
    s_data = local;
    xSemaphoreGive(s_lock);
    return true;
}

/* ---- M1: reading actual values ---------------------------------------- */

/* Which parsed usage feeds which member of ups_data_t.
 *
 * Collection-qualified entries must come first: Voltage means input, output or
 * battery voltage depending on the collection it sits in, and a real APC
 * reports it in all three. The lookup below takes the first entry that matches,
 * so order is behaviour, not taste. */
#define PWR HID_PAGE_POWER_DEVICE
#define BAT HID_PAGE_BATTERY_SYSTEM

typedef struct {
    uint16_t page, usage, collection;
    size_t   offset;            /* offsetof() into ups_data_t */
} value_bind_t;

static const value_bind_t s_values[] = {
    { PWR, 0x30, HID_COLL_INPUT,   offsetof(ups_data_t, input_voltage)      },
    { PWR, 0x30, HID_COLL_OUTPUT,  offsetof(ups_data_t, output_voltage)     },
    { PWR, 0x30, HID_COLL_BATTERY, offsetof(ups_data_t, battery_voltage)    },
    { PWR, 0x32, HID_COLL_INPUT,   offsetof(ups_data_t, input_frequency)    },
    { BAT, 0x66, HID_COLL_NONE,    offsetof(ups_data_t, battery_charge)     },
    { BAT, 0x68, HID_COLL_NONE,    offsetof(ups_data_t, battery_runtime)    },
    { PWR, 0x35, HID_COLL_NONE,    offsetof(ups_data_t, ups_load)           },
    { PWR, 0x34, HID_COLL_NONE,    offsetof(ups_data_t, ups_realpower)      },
    { PWR, 0x44, HID_COLL_NONE,    offsetof(ups_data_t, ups_realpower_nom)  },
    { PWR, 0x33, HID_COLL_NONE,    offsetof(ups_data_t, ups_apparentpower)  },
};
#define VALUE_COUNT (sizeof(s_values) / sizeof(s_values[0]))

/* Status flags. `invert` covers ACPresent, which is TRUE when the UPS is on
 * line power -- the opposite sense to every other flag here. Getting that
 * backwards reports OB to Home Assistant while the mains is perfectly fine,
 * which is worse than reporting nothing. */
typedef struct {
    uint16_t page, usage;
    uint32_t bit;
    bool     invert;
} status_bind_t;

static const status_bind_t s_flags[] = {
    { BAT, 0xD0, UPS_STATUS_ONLINE,       false },  /* ACPresent            */
    { BAT, 0xD0, UPS_STATUS_ONBATT,       true  },  /* ...and its negation  */
    { BAT, 0x44, UPS_STATUS_CHARGING,     false },
    { BAT, 0x45, UPS_STATUS_DISCHARGE,    false },
    { BAT, 0x42, UPS_STATUS_LOWBATT,      false },  /* BelowRemainingCapLimit */
    { BAT, 0x4B, UPS_STATUS_REPLACEBATT,  false },
    { PWR, 0x65, UPS_STATUS_OVERLOAD,     false },
};
#define FLAG_COUNT (sizeof(s_flags) / sizeof(s_flags[0]))

/* The set of Feature reports worth fetching, worked out once at enumeration so
 * the poll loop does no searching. A UPS puts its values across many reports --
 * the captured APC spreads them over 44 IDs -- and fetching all of them every
 * two seconds would be pointless traffic. */
/* Nine reports carry the readings on the bench APC, and the four controls
 * add up to four more. */
#define MAX_POLL_REPORTS 16
/* Payload bytes one feature read carries: a 64-byte packet less the ID. */
#define REPORT_BYTES_MAX 63
static uint8_t s_poll_rid[MAX_POLL_REPORTS];
static uint8_t s_poll_bytes[MAX_POLL_REPORTS];      /* <= REPORT_BYTES_MAX */
static size_t  s_poll_count;

static void note_report(const hid_field_t *f)
{
    if (!f || f->item_type != HID_ITEM_FEATURE) return;
    uint32_t need = ((uint32_t)f->bit_offset + f->bit_size + 7) / 8;
    /* A field past the end of what one read carries is not read at all,
     * rather than wrapping this byte count and reading the wrong bytes. */
    if (need > REPORT_BYTES_MAX) {
        ESP_LOGW(TAG, "report %u: a field ends at byte %u, past the %d read; skipped",
                 f->report_id, (unsigned)need, REPORT_BYTES_MAX);
        return;
    }
    for (size_t i = 0; i < s_poll_count; i++) {
        if (s_poll_rid[i] == f->report_id) {
            if (need > s_poll_bytes[i]) s_poll_bytes[i] = (uint8_t)need;
            return;
        }
    }
    if (s_poll_count >= MAX_POLL_REPORTS) return;
    s_poll_rid[s_poll_count]   = f->report_id;
    s_poll_bytes[s_poll_count] = (uint8_t)need;
    s_poll_count++;
}

/* Did a reply of `len` payload bytes carry all of this field? hid_extract()
 * reads missing bits as zero, and a zero ACPresent is "on battery": a UPS
 * answering short would have been reported as on battery with the mains up. */
static bool field_fits(const hid_field_t *f, int len)
{
    return len > 0 && ((uint32_t)f->bit_offset + f->bit_size + 7) / 8 <= (uint32_t)len;
}

/* Prefer a Feature report: that is where a UPS keeps the authoritative value.
 * An Input report of the same usage is the same datum but only arrives when the
 * device feels like sending it. */
static const hid_field_t *pick(uint16_t page, uint16_t usage, uint16_t coll)
{
    const hid_field_t *f = (coll == HID_COLL_NONE)
                         ? hid_find_typed(&s_map, page, usage, HID_ITEM_FEATURE)
                         : hid_find_in(&s_map, page, usage, coll);
    if (f && f->item_type != HID_ITEM_FEATURE) return NULL;
    return f;
}

static void build_poll_plan(void)
{
    s_poll_count = 0;
    for (size_t i = 0; i < VALUE_COUNT; i++) {
        note_report(pick(s_values[i].page, s_values[i].usage,
                         s_values[i].collection));
    }
    for (size_t i = 0; i < FLAG_COUNT; i++) {
        note_report(pick(s_flags[i].page, s_flags[i].usage, HID_COLL_NONE));
    }
    /* Controls are polled too, so the page shows what the UPS believes rather
     * than what we last asked it for. A beeper muted from the front panel
     * should show as muted here. */
    for (size_t i = 0; i < CTRL_COUNT; i++) {
        note_report(s_ctrl_field[i]);
    }
    note_report(s_date_field);

    char list[96];
    int o = 0;
    for (size_t i = 0; i < s_poll_count && o < (int)sizeof(list) - 8; i++) {
        o += snprintf(list + o, sizeof(list) - o, "%s%u",
                      i ? "," : "", s_poll_rid[i]);
    }
    ESP_LOGI(TAG, "polling %u feature report(s): %s",
             (unsigned)s_poll_count, s_poll_count ? list : "(none)");
}

/* GET_REPORT(Feature, id). Returns payload bytes with the report ID stripped,
 * which is the form hid_extract expects. */
static int get_feature(uint8_t report_id, uint8_t *out, uint8_t want)
{
    uint8_t buf[REPORT_BYTES_MAX + 1];
    int len = report_wire_len(report_id, want);
    if (len > (int)sizeof(buf)) len = sizeof(buf);

    int n = ctrl_in(0xA1, REQ_GET_REPORT,
                    (uint16_t)((REPORT_TYPE_FEATURE << 8) | report_id),
                    s_hid_iface, (uint16_t)len, buf);
    if (n <= 0) return -1;
    /* With Report IDs the device echoes the ID as byte 0 and bit offsets
     * start after it; without them there is no prefix. See report_io.h. */
    return report_payload(buf, n, report_id, out, want);
}

/* The every-poll reads' bytes (poll_values), kept so NUT's table variables
 * and status rows on the same reports use them rather than lag behind on the
 * slower rotation. A BE600M1's input.voltage stayed at 122 V through a whole
 * outage before this: the table's copy was minutes stale, the fixed one not. */
static uint8_t s_qpay[MAX_POLL_REPORTS][REPORT_BYTES_MAX];
static int     s_qgot[MAX_POLL_REPORTS];

/* This poll's bytes for report `rid`, if the every-poll set read at least
 * `need` of them; NULL otherwise. */
static const uint8_t *quick_payload(uint8_t rid, uint32_t need, int *len)
{
    for (size_t i = 0; i < s_poll_count; i++) {
        if (s_poll_rid[i] != rid) continue;
        if (s_qgot[i] <= 0 || (uint32_t)s_qgot[i] < need) return NULL;
        *len = s_qgot[i];
        return s_qpay[i];
    }
    return NULL;
}

/* ---- NUT's variable tables (ups_vartab.h) ------------------------------
 *
 * Everything beyond the handful of values above: a UPS gets the rows of the
 * NUT subdriver that claims its USB ID, each matched against its own
 * descriptor by exact path, and every one it actually has is published. They
 * are read a few reports per poll, round-robin, not all every two seconds:
 * an APC spreads its values over 40-odd report IDs. Static ones (ratings,
 * dates, names) are read once. */

#define MAX_VARS            64
#define MAX_VAR_REPORTS     48
#define VAR_READS_PER_POLL  4

typedef struct {
    const ups_vartab_row_t *row;
    const hid_field_t      *f;
    bool                    valid;
    char                    value[32];
    const hid_field_t      *fin;   /* its Input twin (same path), for events */
} var_slot_t;

static var_slot_t  s_vars[MAX_VARS];
static size_t      s_var_count;             /* readers take s_lock */
static uint8_t     s_var_rid[MAX_VAR_REPORTS];
static uint8_t     s_var_bytes[MAX_VAR_REPORTS];
static bool        s_var_static_done[MAX_VAR_REPORTS];
static size_t      s_var_rcount, s_var_next;
static const char *s_var_table = "none";
static ups_vars_state_t s_var_state;       /* ups_task only */

/* APC Modbus over USB (apc_modbus.h): the readings a Smart-UPS keeps out of
 * HID, published after NUT's table so a name the table has stays the table's.
 * Cleared with the table. Only ups_task writes; readers take s_lock. */
static apcmb_sched_t   s_mbs;               /* when to ask: apc_modbus.h */
static int64_t         s_mb_sent_us;
static apcmb_reading_t s_mb_r;
static apcmb_var_t     s_mb_vars[APCMB_MAX_VARS];
static size_t          s_mb_nvars;

/* What went over the wire, for /api/modbus: no Smart-UPS with Modbus has been
 * on the bench, so a tester's capture is how its replies get checked against
 * NUT's. The last MB_TRACE exchanges with their raw reply frames, the last
 * raw registers, and counters since attach. Written by ups_task under s_lock. */
#define MB_TRACE 16
enum { MBT_OK, MBT_TIMEOUT, MBT_SEND_FAILED, MBT_EXCEPTION, MBT_GONE };
typedef struct {
    uint32_t t_ms;                  /* since boot */
    uint16_t addr, count;
    uint16_t ms;                    /* request to reply, or to giving up */
    uint8_t  attempt, result, exception, foreign, other;
    uint8_t  len;                   /* bytes of frame below */
    uint8_t  frame[3 + 2 * APCMB_DYN_COUNT];
} mb_trace_t;
static mb_trace_t s_mbt[MB_TRACE];
static size_t     s_mbt_next, s_mbt_n;
static struct { uint32_t req, ok, timeout, send_failed, exception, foreign; } s_mbc;
static uint16_t   s_mb_nom_raw[APCMB_NOM_COUNT], s_mb_dyn_raw[APCMB_DYN_COUNT];
static bool       s_mb_nom_have, s_mb_dyn_have;
static uint32_t   s_mb_dyn_ms;

/* NUT's ups.status (ups_nutstatus.h), from NUT's status rows for this UPS.
 * Used only when a bound row reports the power state (online/offline): a
 * partial table must never make ups.status worse than the fixed flags. */
#define MAX_ST_SLOTS    32
#define MAX_ST_REPORTS  8
static struct { const ups_st_row_t *row; const hid_field_t *f, *fin; } s_st[MAX_ST_SLOTS];
static size_t   s_st_count;
static uint8_t  s_st_rid[MAX_ST_REPORTS], s_st_bytes[MAX_ST_REPORTS];
static size_t   s_st_rcount;
static bool     s_st_power;                 /* a row gives online/offline */
static uint32_t s_st_bits;                  /* NUT's ups_status: persists */
static bool     s_nst_valid;                /* readers take s_lock */
static char     s_nst_status[64], s_nst_alarm[200];
static const char *s_nst_reason;

/* Another table variable's current value, for the corrections that depend on
 * one (a CyberPower's battery.voltage on its battery.voltage.nominal). Runs in
 * ups_task, the only writer of s_vars, so it reads them without the lock. */
static bool var_lookup(void *ctx, const char *name, double *v)
{
    (void)ctx;
    for (size_t i = 0; i < s_var_count; i++) {
        if (s_vars[i].valid && !strcmp(s_vars[i].row->name, name)) {
            char *end;
            double d = strtod(s_vars[i].value, &end);
            if (end == s_vars[i].value) return false;
            *v = d;
            return true;
        }
    }
    return false;
}

static void vars_clear(void)
{
    xSemaphoreTake(s_lock, portMAX_DELAY);
    s_var_count = 0;
    s_nst_valid = false;
    xSemaphoreGive(s_lock);
    s_st_count = s_st_rcount = 0;
    s_st_power = false;
    s_st_bits = 0;
    s_var_rcount = s_var_next = 0;
    memset(s_var_static_done, 0, sizeof(s_var_static_done));
    s_var_table = "none";
    xSemaphoreTake(s_lock, portMAX_DELAY);
    s_mb_nvars = 0;
    xSemaphoreGive(s_lock);
    s_mb = false;
    apcmb_sched_init(&s_mbs);
    xSemaphoreTake(s_lock, portMAX_DELAY);
    s_mbt_next = s_mbt_n = 0;
    memset(&s_mbc, 0, sizeof(s_mbc));
    s_mb_nom_have = s_mb_dyn_have = false;
    xSemaphoreGive(s_lock);
}

static void bind_vars(uint16_t vid, uint16_t pid)
{
    vars_clear();
    int sub = ups_vars_sub_for(vid, pid);
    size_t n;
    const uint16_t *list = ups_vartab_list(sub, &n);
    size_t count = 0;
    for (size_t i = 0; i < n && count < MAX_VARS; i++) {
        const ups_vartab_row_t *r = &ups_vartab_rows[list[i]];
        bool have = false;                  /* the first row a UPS has wins */
        for (size_t k = 0; k < count && !have; k++) have = !strcmp(s_vars[k].row->name, r->name);
        if (have) continue;
        const hid_field_t *f = NULL;
        for (size_t k = 0; k < s_map.count && !f; k++) {
            const hid_field_t *c = &s_map.fields[k];
            if (c->item_type == HID_ITEM_FEATURE && ups_vars_row_matches(&s_map, c, r)) f = c;
        }
        if (!f) continue;
        uint32_t need = ((uint32_t)f->bit_offset + f->bit_size + 7) / 8;
        if (need > REPORT_BYTES_MAX) continue;
        size_t j;
        for (j = 0; j < s_var_rcount && s_var_rid[j] != f->report_id; j++) { }
        if (j == s_var_rcount) {
            if (s_var_rcount >= MAX_VAR_REPORTS) continue;
            s_var_rid[j] = f->report_id;
            s_var_bytes[j] = 0;
            s_var_rcount++;
        }
        if (need > s_var_bytes[j]) s_var_bytes[j] = (uint8_t)need;
        s_vars[count].row = r;
        s_vars[count].f = f;
        s_vars[count].fin = NULL;
        for (size_t k = 0; k < s_map.count; k++) {
            const hid_field_t *c = &s_map.fields[k];
            if (c->item_type == HID_ITEM_INPUT && ups_vars_row_matches(&s_map, c, r)) { s_vars[count].fin = c; break; }
        }
        s_vars[count].valid = false;
        s_vars[count].value[0] = '\0';
        count++;
    }
    /* NUT's status rows: the first path this UPS has, per row, in order. */
    size_t sn;
    const uint16_t *sl = ups_st_list(sub, &sn);
    for (size_t i = 0; i < sn && s_st_count < MAX_ST_SLOTS; i++) {
        const ups_st_row_t *r = &ups_st_rows[sl[i]];
        const hid_field_t *f = NULL;
        for (size_t k = 0; k < s_map.count && !f; k++) {
            const hid_field_t *c = &s_map.fields[k];
            if (c->item_type == HID_ITEM_FEATURE && ups_vars_st_matches(&s_map, c, r)) f = c;
        }
        if (!f) continue;
        uint32_t need = ((uint32_t)f->bit_offset + f->bit_size + 7) / 8;
        if (need > REPORT_BYTES_MAX) continue;
        size_t j;
        for (j = 0; j < s_st_rcount && s_st_rid[j] != f->report_id; j++) { }
        if (j == s_st_rcount) {
            if (s_st_rcount >= MAX_ST_REPORTS) continue;
            s_st_rid[j] = f->report_id; s_st_bytes[j] = 0; s_st_rcount++;
        }
        if (need > s_st_bytes[j]) s_st_bytes[j] = (uint8_t)need;
        s_st[s_st_count].row = r;
        s_st[s_st_count].f = f;
        s_st[s_st_count].fin = NULL;
        for (size_t k = 0; k < s_map.count; k++) {
            const hid_field_t *c = &s_map.fields[k];
            if (c->item_type == HID_ITEM_INPUT && ups_vars_st_matches(&s_map, c, r)) { s_st[s_st_count].fin = c; break; }
        }
        s_st_count++;
        for (size_t k = 0; k < r->nlk; k++) {
            if (r->lk[k].token == NST_ONLINE || r->lk[k].token == NST_OFFLINE) s_st_power = true;
        }
    }
    ESP_LOGI(TAG, "%u NUT status rows over %u reports%s", (unsigned)s_st_count,
             (unsigned)s_st_rcount, s_st_power ? "" : " (no power state: fixed flags kept)");
    s_var_table = sub >= 0 ? ups_vartab_subs[sub].name : "common";
    ups_vars_state_init(&s_var_state, vid, pid, var_lookup, NULL);
    xSemaphoreTake(s_lock, portMAX_DELAY);
    s_var_count = count;
    xSemaphoreGive(s_lock);
    ESP_LOGI(TAG, "%u NUT variables from NUT's %s table, over %u reports",
             (unsigned)count, s_var_table, (unsigned)s_var_rcount);
}

static void st_apply(const ups_st_row_t *r, long v);
static void nst_publish(float charge);

/* NUT's status rows, every poll: each value through its lookup to a token,
 * then usbhid-ups's own ups_status_set(). Not while ups_task is holding the
 * status through a post-self-test glitch (status_hold.h): the words NUT would
 * build from an all-zero read are exactly what that hold exists to stop. */
static void poll_status(float charge)
{
    if (!s_st_count || !s_st_power) return;
    for (size_t j = 0; j < s_st_rcount; j++) {
        static uint8_t buf[REPORT_BYTES_MAX];
        int got = 0;
        const uint8_t *pl = quick_payload(s_st_rid[j], s_st_bytes[j], &got);
        if (!pl) { got = get_feature(s_st_rid[j], buf, s_st_bytes[j]); pl = buf; }
        if (got <= 0) continue;
        for (size_t k = 0; k < s_st_count; k++) {
            if (s_st[k].f->report_id != s_st_rid[j] || !field_fits(s_st[k].f, got)) continue;
            st_apply(s_st[k].row, lroundf(hid_extract(s_st[k].f, pl, (size_t)got)));
        }
    }
    nst_publish(charge);
}

/* One status row's value through its lookup, as NUT's process_boolean_info. */
static void st_apply(const ups_st_row_t *r, long v)
{
    if (r->nlk == 1 && r->lk[0].value == UPS_ST_NONZERO) {       /* Liebert */
        ups_nutstatus_apply(&s_st_bits, r->lk[0].token, v == 0);
        return;
    }
    for (size_t e = 0; e < r->nlk; e++) {
        if (r->lk[e].value == v) {
            ups_nutstatus_apply(&s_st_bits, r->lk[e].token, r->lk[e].clear);
            return;
        }
    }
}

/* ups_status_set() and ups_alarm_set() on the current tokens, published
 * unless the post-self-test glitch hold is on. */
static void nst_publish(float charge)
{
    char st[sizeof(s_nst_status)], al[sizeof(s_nst_alarm)];
    ups_nutstatus_string(s_st_bits, ups_valid(charge) ? (int)lroundf(charge) : -1, st, sizeof(st));
    ups_nutstatus_alarm(s_st_bits, al, sizeof(al));
    xSemaphoreTake(s_lock, portMAX_DELAY);
    if (!s_data.status_hold_since_us) {
        strlcpy(s_nst_status, st, sizeof(s_nst_status));
        strlcpy(s_nst_alarm, al, sizeof(s_nst_alarm));
        s_nst_reason = ups_nutstatus_transfer_reason(s_st_bits);
        s_nst_valid = true;
    }
    xSemaphoreGive(s_lock);
}

/* An Input report from the interrupt pipe: every status row and table
 * variable whose Input twin is in it, updated now rather than at the next
 * poll. With Report IDs in use, byte 0 is the ID. */
static void ipipe_process(const uint8_t *d, int n)
{
    if (n <= 0) return;
    bool ids = false;
    for (size_t i = 0; i < s_map.count && !ids; i++) ids = s_map.fields[i].report_id != 0;
    uint8_t rid = ids ? d[0] : 0;
    const uint8_t *pl = ids ? d + 1 : d;
    int pll = ids ? n - 1 : n;
    if (pll <= 0) return;
    static uint32_t events;
    if (events++ == 0) ESP_LOGI(TAG, "interrupt pipe: first report (ID %u, %d bytes)", rid, n);
    bool st = false;
    for (size_t k = 0; k < s_st_count; k++) {
        const hid_field_t *fi = s_st[k].fin;
        if (!fi || fi->report_id != rid || !field_fits(fi, pll)) continue;
        st_apply(s_st[k].row, lroundf(hid_extract(fi, pl, (size_t)pll)));
        st = true;
    }
    for (size_t k = 0; k < s_var_count; k++) {
        var_slot_t *sl = &s_vars[k];
        if (!sl->fin || sl->fin->report_id != rid || sl->row->conv == VCONV_STRINGID ||
            !field_fits(sl->fin, pll)) continue;
        char buf[sizeof(sl->value)];
        if (!ups_vars_format(&s_var_state, sl->row, sl->fin, pl, pll, buf, sizeof(buf))) continue;
        xSemaphoreTake(s_lock, portMAX_DELAY);
        sl->valid = true;
        strlcpy(sl->value, buf, sizeof(sl->value));
        xSemaphoreGive(s_lock);
    }
    if (st && s_st_power) nst_publish(s_data.battery_charge);
}

bool ups_hid_nut_status(char *status, size_t scap, char *alarm, size_t acap, const char **reason)
{
    if (!s_lock) return false;
    xSemaphoreTake(s_lock, portMAX_DELAY);
    bool ok = s_nst_valid;
    if (ok) {
        strlcpy(status, s_nst_status, scap);
        strlcpy(alarm, s_nst_alarm, acap);
        *reason = s_nst_reason;
    }
    xSemaphoreGive(s_lock);
    return ok;
}

/* A few more reports each poll, round-robin. Runs only in ups_task. */
static void update_slots(uint8_t rid, const uint8_t *pl, int got, bool *all_static);

static void poll_vars(void)
{
    /* Reports the every-poll set already read this time: as fresh as the
     * fixed values, and no extra USB traffic. */
    for (size_t i = 0; i < s_var_rcount; i++) {
        int got = 0;
        const uint8_t *pl = quick_payload(s_var_rid[i], s_var_bytes[i], &got);
        if (pl) update_slots(s_var_rid[i], pl, got, NULL);
    }
    int reads = 0;
    for (size_t tries = 0; reads < VAR_READS_PER_POLL && tries < s_var_rcount; tries++) {
        size_t i = s_var_next;
        s_var_next = (s_var_next + 1) % s_var_rcount;
        if (s_var_static_done[i]) continue;
        int qlen;
        if (quick_payload(s_var_rid[i], s_var_bytes[i], &qlen)) continue;   /* done above */
        static uint8_t pl[REPORT_BYTES_MAX];
        int got = get_feature(s_var_rid[i], pl, s_var_bytes[i]);
        reads++;
        bool all_static = true;
        update_slots(s_var_rid[i], pl, got, &all_static);
        if (got > 0 && all_static) s_var_static_done[i] = true;
    }
}

/* Every table variable on report `rid`, from its bytes (`got` <= 0: a failed
 * read, so they go invalid). `all_static` is cleared if any is not static;
 * NULL means this is the every-poll path, where a string that already has a
 * value is not fetched again: strings do not change, USB reads cost. */
static void update_slots(uint8_t rid, const uint8_t *pl, int got, bool *all_static)
{
    for (size_t k = 0; k < s_var_count; k++) {
        var_slot_t *sl = &s_vars[k];
        if (sl->f->report_id != rid) continue;
        if (all_static && sl->row->poll != VPOLL_STATIC) *all_static = false;
        if (!all_static && sl->row->conv == VCONV_STRINGID && sl->valid) continue;
        char buf[sizeof(sl->value)];
        bool ok = false;
        bool fits = field_fits(sl->f, got);
        if (fits && sl->row->conv == VCONV_STRINGID) {
            /* A string descriptor index: fetched here, where USB is. */
            long ix = (long)hid_extract_raw(sl->f, pl, (size_t)got);
            if (ix > 0 && ix <= 255) { read_string((uint8_t)ix, buf, sizeof(buf)); ok = buf[0]; }
        } else if (fits) {
            ok = ups_vars_format(&s_var_state, sl->row, sl->f, pl, got, buf, sizeof(buf));
        }
        xSemaphoreTake(s_lock, portMAX_DELAY);
        sl->valid = ok;
        if (ok) strlcpy(sl->value, buf, sizeof(sl->value));
        xSemaphoreGive(s_lock);
    }
}

/* ---- APC Modbus over USB ----------------------------------------------
 *
 * See apc_modbus.h. A request goes out as an Output report, on the interrupt
 * OUT endpoint as libmodbus sends it, or by SET_REPORT where the interface has
 * none. The reply comes back as Input reports on the interrupt pipe, which is
 * already listening: while waiting, this takes the Modbus ones and hands every
 * other report to ipipe_process() as the main loop would.
 *
 * Bounded like tl_xfer(): NUT's 500 ms response timeout and 3 tries; when to
 * try at all is apcmb_sched_t's. A command from the page or NUT waits for
 * ups_task behind this, with a 5 s timeout, so a waiting command ends the
 * read at once (APCMB_R_YIELD) rather than queue behind three timeouts: a
 * self-test reported "timed out" and then run anyway is worse than a Modbus
 * reading two seconds late. */
static bool mb_cmd_waiting(void)
{
    return s_cmd_q && uxQueueMessagesWaiting(s_cmd_q) > 0;
}

#define MB_TIMEOUT_MS       500
#define MB_TRIES            3
#define MB_GAP_US           35000                   /* NUT's inter-frame delay */

static bool intr_out(const uint8_t *data, size_t len)
{
    if (!s_intr_done) s_intr_done = xSemaphoreCreateBinary();
    if (!s_intr_done) return false;
    usb_transfer_t *xfer = NULL;
    if (usb_host_transfer_alloc(len, 0, &xfer) != ESP_OK) return false;
    memcpy(xfer->data_buffer, data, len);
    xfer->device_handle    = s_dev;
    xfer->bEndpointAddress = s_intr_out_ep;
    xfer->num_bytes        = len;
    xfer->callback         = ctrl_cb;
    xfer->context          = s_intr_done;
    xSemaphoreTake(s_intr_done, 0);
    if (usb_host_transfer_submit(xfer) != ESP_OK) {
        usb_host_transfer_free(xfer);
        return false;
    }
    bool done = false;
    for (int waited = 0; waited < MB_TIMEOUT_MS && !done; waited += 10) {
        usb_host_client_handle_events(s_client, pdMS_TO_TICKS(10));
        done = xSemaphoreTake(s_intr_done, 0) == pdTRUE;
    }
    if (!done) {
        /* Cancelled and awaited before it is freed, as intr_in() does. */
        usb_host_endpoint_halt(s_dev, s_intr_out_ep);
        usb_host_endpoint_flush(s_dev, s_intr_out_ep);
        for (int waited = 0; waited < 500 && !done; waited += 10) {
            usb_host_client_handle_events(s_client, pdMS_TO_TICKS(10));
            done = xSemaphoreTake(s_intr_done, 0) == pdTRUE;
        }
        usb_host_endpoint_clear(s_dev, s_intr_out_ep);
        if (!done) {
            ESP_LOGE(TAG, "interrupt OUT transfer would not cancel; leaking %u bytes",
                     (unsigned)len);
            return false;
        }
        usb_host_transfer_free(xfer);
        return false;
    }
    bool ok = xfer->status == USB_TRANSFER_STATUS_COMPLETED;
    usb_host_transfer_free(xfer);
    return ok;
}

static bool mb_send(const uint8_t rep[APCMB_REPORT])
{
    if (s_intr_out_ep) return intr_out(rep, APCMB_REPORT);
    return ctrl_out(0x21, REQ_SET_REPORT, (uint16_t)((REPORT_TYPE_OUTPUT << 8) | rep[0]),
                    s_hid_iface, rep, APCMB_REPORT);
}

/* The next report off the interrupt pipe, if one has arrived; the pipe is
 * listening again before this returns. */
static int mb_take(uint8_t *buf)
{
    int n = 0;
    if (s_ipipe_ready) {
        n = s_ipipe_len;
        memcpy(buf, s_ipipe_buf, (size_t)n);
        s_ipipe_ready = false;
    }
    ipipe_kick();
    return n;
}

static void mb_record(const mb_trace_t *e)
{
    xSemaphoreTake(s_lock, portMAX_DELAY);
    s_mbt[s_mbt_next] = *e;
    s_mbt_next = (s_mbt_next + 1) % MB_TRACE;
    if (s_mbt_n < MB_TRACE) s_mbt_n++;
    s_mbc.req++;
    switch (e->result) {
    case MBT_OK:          s_mbc.ok++; break;
    case MBT_TIMEOUT:     s_mbc.timeout++; break;
    case MBT_SEND_FAILED: s_mbc.send_failed++; break;
    case MBT_EXCEPTION:   s_mbc.exception++; break;
    default: break;
    }
    s_mbc.foreign += e->foreign;
    if (e->result == MBT_OK && e->addr == APCMB_NOM_ADDR) {
        for (int k = 0; k < APCMB_NOM_COUNT; k++)
            s_mb_nom_raw[k] = (uint16_t)(e->frame[3 + 2 * k] << 8 | e->frame[4 + 2 * k]);
        s_mb_nom_have = true;
    } else if (e->result == MBT_OK && e->addr == APCMB_DYN_ADDR) {
        for (int k = 0; k < APCMB_DYN_COUNT; k++)
            s_mb_dyn_raw[k] = (uint16_t)(e->frame[3 + 2 * k] << 8 | e->frame[4 + 2 * k]);
        s_mb_dyn_have = true;
        s_mb_dyn_ms = e->t_ms;
    }
    xSemaphoreGive(s_lock);
}

static apcmb_result_t mb_read(uint16_t addr, uint16_t count, uint16_t *regs, int tries)
{
    uint8_t req[APCMB_REPORT], buf[sizeof(s_ipipe_buf)];
    for (int t = 0; t < tries; t++) {
        if (!s_ipipe_on || s_dev_gone || !s_dev) return APCMB_R_FAIL;
        if (mb_cmd_waiting()) return APCMB_R_YIELD;
        int64_t gap = s_mb_sent_us + MB_GAP_US - esp_timer_get_time();
        if (gap > 0) vTaskDelay(pdMS_TO_TICKS(gap / 1000 + 1));
        mb_trace_t e = { .addr = addr, .count = count, .attempt = (uint8_t)(t + 1) };
        /* Whatever is already waiting predates this request. */
        int n;
        while ((n = mb_take(buf)) > 0) {
            if (buf[0] != s_mb_from) ipipe_process(buf, n);
            else if (e.foreign < 255) e.foreign++;
        }
        apcmb_build_read(s_mb_to, APCMB_SLAVE, addr, count, req);
        s_mb_sent_us = esp_timer_get_time();
        e.t_ms = (uint32_t)(s_mb_sent_us / 1000);
        if (!mb_send(req)) {
            e.result = MBT_SEND_FAILED;
            e.ms = (uint16_t)((esp_timer_get_time() - s_mb_sent_us) / 1000);
            mb_record(&e);
            continue;
        }

        apcmb_rx_t rx;
        apcmb_rx_init(&rx, APCMB_SLAVE, count);
        e.result = MBT_TIMEOUT;
        for (int waited = 0; waited < MB_TIMEOUT_MS && e.result == MBT_TIMEOUT; waited += 10) {
            usb_host_client_handle_events(s_client, pdMS_TO_TICKS(10));
            if (s_dev_gone) { e.result = MBT_GONE; break; }
            if (mb_cmd_waiting()) break;    /* recorded as a timeout, then yields */
            n = mb_take(buf);
            if (n <= 0) continue;
            if (buf[0] != s_mb_from) {
                ipipe_process(buf, n);
                if (e.other < 255) e.other++;
                continue;
            }
            apcmb_rx_status_t st = apcmb_rx_feed(&rx, buf + 1, (size_t)(n - 1), regs);
            if (st == APCMB_DONE) e.result = MBT_OK;
            else if (st == APCMB_EXCEPTION) e.result = MBT_EXCEPTION;
            else if (st == APCMB_FOREIGN && e.foreign < 255) e.foreign++;
        }
        e.ms = (uint16_t)((esp_timer_get_time() - s_mb_sent_us) / 1000);
        e.exception = rx.exception;
        if (e.result == MBT_EXCEPTION) { e.frame[0] = APCMB_SLAVE; e.frame[1] = 0x83; e.frame[2] = rx.exception; e.len = 3; }
        else {
            e.len = (uint8_t)(rx.len < sizeof(e.frame) ? rx.len : sizeof(e.frame));
            memcpy(e.frame, rx.frame, e.len);
        }
        mb_record(&e);
        if (e.result == MBT_OK) return APCMB_R_OK;
        if (e.result == MBT_GONE) return APCMB_R_FAIL;
        if (e.result == MBT_EXCEPTION) {
            ESP_LOGW(TAG, "APC Modbus: read of %u+%u refused, exception %u",
                     addr, count, rx.exception);
            return APCMB_R_FAIL;            /* a retry gets the same answer */
        }
        if (mb_cmd_waiting()) return APCMB_R_YIELD;
    }
    return APCMB_R_FAIL;
}

/* Does the descriptor give this ups_data_t member a HID field? Decided by
 * the binding, not by whether a value happens to be there: one failed HID
 * read left a member empty for a poll, and Modbus then claimed it and the two
 * took turns writing it. */
static bool hid_has_value(size_t offset)
{
    for (size_t v = 0; v < VALUE_COUNT; v++) {
        if (s_values[v].offset == offset &&
            pick(s_values[v].page, s_values[v].usage, s_values[v].collection)) return true;
    }
    return false;
}

/* Fill a ups_data_t reading from Modbus, unless HID has it. */
static void mb_field(size_t offset, double v)
{
    if (hid_has_value(offset)) return;
    *(float *)((char *)&s_data + offset) = v == APCMB_ABSENT ? UPS_VALUE_ABSENT : (float)v;
}

/* The current reading, or none (`live` false), to the variable list and to
 * the ups_data_t fields HID does not fill. */
static void mb_publish(bool live)
{
    apcmb_var_t v[APCMB_MAX_VARS];
    size_t n = live ? apcmb_vars(&s_mb_r, v) : 0, keep = 0;
    for (size_t i = 0; i < n; i++) {
        bool table = false;                 /* NUT's table binds it: the table's */
        for (size_t k = 0; k < s_var_count && !table; k++) table = !strcmp(s_vars[k].row->name, v[i].name);
        if (!table) v[keep++] = v[i];
    }
    apcmb_reading_t none;
    apcmb_reading_init(&none);
    const apcmb_reading_t *r = live ? &s_mb_r : &none;
    xSemaphoreTake(s_lock, portMAX_DELAY);
    memcpy(s_mb_vars, v, keep * sizeof(v[0]));
    s_mb_nvars = keep;
    mb_field(offsetof(ups_data_t, input_voltage),     r->input_voltage);
    mb_field(offsetof(ups_data_t, output_voltage),    r->output_voltage);
    mb_field(offsetof(ups_data_t, ups_load),          r->load);
    mb_field(offsetof(ups_data_t, ups_realpower),     r->realpower);
    mb_field(offsetof(ups_data_t, ups_realpower_nom), r->realpower_nominal);
    mb_field(offsetof(ups_data_t, ups_apparentpower), r->power);
    mb_field(offsetof(ups_data_t, battery_voltage),   r->battery_voltage);
    xSemaphoreGive(s_lock);
}

/* After a good HID poll: the nameplate once, then the dynamic block, as
 * apcmb_sched_t says. */
static void mb_poll(void)
{
    if (!s_mb || s_legacy || !s_ipipe_on) return;
    int64_t now = esp_timer_get_time();
    apcmb_step_t step = apcmb_sched_step(&s_mbs, now);
    if (step == APCMB_IDLE) return;
    uint16_t regs[APCMB_MAX_REGS];

    if (step == APCMB_PROBE) {
        apcmb_result_t r = mb_read(APCMB_NOM_ADDR, APCMB_NOM_COUNT, regs, 2);
        unsigned ev = apcmb_sched_done(&s_mbs, step, r, now);
        if (ev & APCMB_EV_HINT) {
            ESP_LOGW(TAG, "APC Modbus: no answer. For voltages, turn Modbus on in the "
                          "UPS's menu (Configuration, Modbus, Enable); trying again "
                          "every %lld min", (long long)(APCMB_RETRY_US / 60000000));
        }
        if (!(ev & APCMB_EV_UP)) return;
        apcmb_reading_init(&s_mb_r);
        apcmb_decode_nominal(regs, &s_mb_r);
        ESP_LOGI(TAG, "APC Modbus: answering, %.0f VA / %.0f W",
                 s_mb_r.power_nominal, s_mb_r.realpower_nominal);
    }

    apcmb_result_t r = mb_read(APCMB_DYN_ADDR, APCMB_DYN_COUNT, regs, MB_TRIES);
    unsigned ev = apcmb_sched_done(&s_mbs, APCMB_READ, r, now);
    if (ev & APCMB_EV_DROP) {
        ESP_LOGW(TAG, "APC Modbus: stopped answering; dropping its readings");
        mb_publish(false);
    }
    if (r != APCMB_R_OK) return;
    apcmb_decode_dynamic(regs, &s_mb_r);
    mb_publish(true);
}

/* NUT's table variables, then the APC Modbus ones after them. */
size_t ups_hid_var_count(void)
{
    if (!s_lock) return 0;
    xSemaphoreTake(s_lock, portMAX_DELAY);
    size_t n = s_var_count + s_mb_nvars;
    xSemaphoreGive(s_lock);
    return n;
}

bool ups_hid_var_get(size_t i, const char **name, char *value, size_t cap)
{
    if (!s_lock) return false;
    bool ok = false;
    xSemaphoreTake(s_lock, portMAX_DELAY);
    if (i < s_var_count && s_vars[i].valid) {
        *name = s_vars[i].row->name;        /* flash: valid for ever */
        strlcpy(value, s_vars[i].value, cap);
        ok = true;
    } else if (i >= s_var_count && i - s_var_count < s_mb_nvars) {
        *name = s_mb_vars[i - s_var_count].name;    /* string literals */
        strlcpy(value, s_mb_vars[i - s_var_count].value, cap);
        ok = true;
    }
    xSemaphoreGive(s_lock);
    return ok;
}

bool ups_hid_var_find(const char *name, char *value, size_t cap)
{
    if (!s_lock) return false;
    bool ok = false;
    xSemaphoreTake(s_lock, portMAX_DELAY);
    for (size_t i = 0; i < s_var_count && !ok; i++) {
        if (s_vars[i].valid && !strcmp(s_vars[i].row->name, name)) {
            strlcpy(value, s_vars[i].value, cap);
            ok = true;
        }
    }
    for (size_t i = 0; i < s_mb_nvars && !ok; i++) {
        if (!strcmp(s_mb_vars[i].name, name)) {
            strlcpy(value, s_mb_vars[i].value, cap);
            ok = true;
        }
    }
    xSemaphoreGive(s_lock);
    return ok;
}

const char *ups_hid_var_table(void) { return s_var_table; }

#define J(...) do { if (n < cap) n += (size_t)snprintf(buf + n, cap - n, __VA_ARGS__); } while (0)

size_t ups_hid_modbus_json(char *buf, size_t cap)
{
    static const char *const res[] = { "ok", "timeout", "send_failed", "exception", "gone" };
    size_t n = 0;
    if (!s_lock || !cap) return 0;
    int64_t now = esp_timer_get_time();
    xSemaphoreTake(s_lock, portMAX_DELAY);
    J("{\"transport\":{\"present\":%s", s_mb ? "true" : "false");
    if (s_mb) {
        J(",\"to_ups\":%u,\"from_ups\":%u,\"send\":\"%s\",\"out_ep\":%u,\"in_ep\":%u,"
          "\"in_mps\":%u,\"pipe\":%s",
          s_mb_to, s_mb_from, s_intr_out_ep ? "interrupt_out" : "set_report",
          s_intr_out_ep, s_intr_ep, s_intr_mps, s_ipipe_on ? "true" : "false");
    }
    J("},\"vid\":%u,\"pid\":%u,\"live\":%s,\"fails\":%d,\"next_try_s\":%lld,\"uptime_ms\":%lu,",
      s_data.vid, s_data.pid, s_mbs.live ? "true" : "false", s_mbs.fails,
      (long long)(s_mbs.next_us > now ? (s_mbs.next_us - now) / 1000000 : 0),
      (unsigned long)(now / 1000));
    J("\"counts\":{\"requests\":%lu,\"ok\":%lu,\"timeout\":%lu,\"send_failed\":%lu,"
      "\"exception\":%lu,\"foreign\":%lu},",
      (unsigned long)s_mbc.req, (unsigned long)s_mbc.ok, (unsigned long)s_mbc.timeout,
      (unsigned long)s_mbc.send_failed, (unsigned long)s_mbc.exception, (unsigned long)s_mbc.foreign);
    J("\"nominal_regs\":");
    if (s_mb_nom_have) J("{\"addr\":%d,\"regs\":[%u,%u]},", APCMB_NOM_ADDR, s_mb_nom_raw[0], s_mb_nom_raw[1]);
    else J("null,");
    J("\"dynamic_regs\":");
    if (s_mb_dyn_have) {
        J("{\"addr\":%d,\"t_ms\":%lu,\"regs\":[", APCMB_DYN_ADDR, (unsigned long)s_mb_dyn_ms);
        for (int k = 0; k < APCMB_DYN_COUNT; k++) J("%s%u", k ? "," : "", s_mb_dyn_raw[k]);
        J("]},");
    } else J("null,");
    J("\"vars\":{");
    for (size_t i = 0; i < s_mb_nvars; i++) J("%s\"%s\":\"%s\"", i ? "," : "", s_mb_vars[i].name, s_mb_vars[i].value);
    J("},\"trace\":[");
    for (size_t i = 0; i < s_mbt_n; i++) {      /* oldest first */
        const mb_trace_t *e = &s_mbt[(s_mbt_next + MB_TRACE - s_mbt_n + i) % MB_TRACE];
        J("%s{\"t_ms\":%lu,\"addr\":%u,\"count\":%u,\"attempt\":%u,\"result\":\"%s\","
          "\"ms\":%u,\"foreign\":%u,\"other_reports\":%u,\"reply\":\"",
          i ? "," : "", (unsigned long)e->t_ms, e->addr, e->count, e->attempt,
          e->result < 5 ? res[e->result] : "?", e->ms, e->foreign, e->other);
        for (size_t k = 0; k < e->len; k++) J("%02x", e->frame[k]);
        J("\"}");
    }
    J("]}");
    xSemaphoreGive(s_lock);
    return n < cap ? n : 0;                 /* cut short is not JSON: nothing */
}

#undef J

int ups_hid_modbus_state(void)
{
    if (!s_lock || !s_mb) return 0;
    xSemaphoreTake(s_lock, portMAX_DELAY);
    /* A minute of good reads, or a UPS that is not answering: either is
     * worth a look. Not a probe still under way. */
    bool worth = s_mbc.ok >= 30 || (!s_mbs.live && s_mbc.req >= 2) || !s_ipipe_on;
    xSemaphoreGive(s_lock);
    return worth ? 2 : 1;
}

/* The writable side of the descriptor.
 *
 * Everything here is discovered, never assumed. A UPS with no Test usage gets
 * no test button, and the web UI is driven from these bits rather than from a
 * model name -- the rule the whole HID path follows (CLAUDE.md: the parsing
 * must stay generic rather than hardcoding this model).
 */
typedef struct {
    uint16_t page, usage;
    uint32_t cap;
    const char *what;
} ctrl_bind_t;

static const ctrl_bind_t s_ctrls[] = {
    { HID_PAGE_POWER_DEVICE,   0x58, UPS_CAP_TEST,     "self-test" },
    { HID_PAGE_POWER_DEVICE,   0x5A, UPS_CAP_BEEPER,   "beeper" },
    { HID_PAGE_BATTERY_SYSTEM, 0x29, UPS_CAP_LOWBATT,  "low-battery limit" },
    { HID_PAGE_POWER_DEVICE,   0x57, UPS_CAP_SHUTDOWN, "delayed load shutdown" },
};
_Static_assert(sizeof(s_ctrls) / sizeof(s_ctrls[0]) == CTRL_COUNT,
               "CTRL_COUNT is declared at the top of this file and must match "
               "the table here");

/* s_ctrl_field is resolved once per attach, so a command never re-walks the
 * descriptor. */
/* The HID packed date: bits 0-4 day, 5-8 month, 9-15 year since 1980. A zero
 * field means the UPS has the usage but no value in it, which is common. */
static void decode_mfr_date(uint32_t raw, char *out, size_t cap)
{
    raw &= 0xFFFF;                       /* the field is 16 bits; bound it so
                                          * the year below cannot run away */
    unsigned day = raw & 0x1F, month = (raw >> 5) & 0x0F, year = 1980 + (raw >> 9);
    if (!raw || !day || !month || month > 12 || day > 31 || year > 2107) {
        out[0] = '\0';
        return;
    }
    snprintf(out, cap, "%04u-%02u-%02u", year, month, day);
}

static uint32_t discover_caps(void)
{
    uint32_t caps = 0;
    /* The BATTERY's date: ManufacturerDate inside the Battery collection,
     * which is where NUT's apc-hid.c reads battery.mfr.date. Taking the first
     * one anywhere picked an APC's PowerSummary date, the UPS's own: the
     * bench RS 1000G reported its 2013 build date as the battery's (2014),
     * and "set battery date" wrote over the UPS's date. A UPS with no Battery
     * collection keeps the one it has, as NUT does for CyberPower. */
    s_date_field = pick(HID_PAGE_BATTERY_SYSTEM, 0x85, HID_COLL_BATTERY);
    if (!s_date_field) s_date_field = pick(HID_PAGE_BATTERY_SYSTEM, 0x85, HID_COLL_NONE);
    if (s_date_field) caps |= UPS_CAP_BATTDATE;
    char list[128];
    int o = 0;
    for (size_t i = 0; i < CTRL_COUNT; i++) {
        s_ctrl_field[i] = pick(s_ctrls[i].page, s_ctrls[i].usage, HID_COLL_NONE);
        if (!s_ctrl_field[i]) continue;
        caps |= s_ctrls[i].cap;
        o += snprintf(list + o, sizeof(list) - o, "%s%s",
                      o ? ", " : "", s_ctrls[i].what);
    }
    ESP_LOGI(TAG, "controls this UPS supports: %s", o ? list : "(none)");
    return caps;
}

static const hid_field_t *ctrl_for(uint32_t cap)
{
    for (size_t i = 0; i < CTRL_COUNT; i++) {
        if (s_ctrls[i].cap == cap) return s_ctrl_field[i];
    }
    return NULL;
}

/* SET_REPORT(Feature, id), read-modify-write.
 *
 * A report can carry several fields -- on this APC report 21 holds
 * DelayBeforeShutdown alongside its neighbours -- so writing a freshly zeroed
 * buffer would clobber them. Reading first costs one extra control transfer
 * and means a beeper command cannot set a shutdown timer by accident. */
static bool set_field(const hid_field_t *f, uint32_t value)
{
    if (!f || f->item_type != HID_ITEM_FEATURE) return false;

    size_t bytes = (size_t)((f->bit_offset + f->bit_size + 7) / 8);
    if (bytes == 0 || bytes > REPORT_BYTES_MAX) return false;

    uint8_t buf[REPORT_BYTES_MAX] = {0};
    int got = get_feature(f->report_id, buf, (uint8_t)bytes);
    if (got < (int)bytes) {
        ESP_LOGW(TAG, "report %u did not read back, refusing to write it",
                 f->report_id);
        return false;
    }

    for (uint16_t b = 0; b < f->bit_size; b++) {
        uint16_t bit = f->bit_offset + b;
        uint8_t  mask = (uint8_t)(1u << (bit % 8));
        if (value & (1u << b)) buf[bit / 8] |= mask;
        else                   buf[bit / 8] &= (uint8_t)~mask;
    }

    /* Prefixed with the ID exactly as GET_REPORT returned it, or not at all. */
    uint8_t wire[REPORT_BYTES_MAX + 1];
    int wlen = report_wire(f->report_id, buf, (int)bytes, wire);
    return ctrl_out(0x21, REQ_SET_REPORT,
                    (uint16_t)((REPORT_TYPE_FEATURE << 8) | f->report_id),
                    s_hid_iface, wire, (uint16_t)wlen);
}

/* Fetch every planned report and fill `d`. Returns true if at least one report
 * came back -- a UPS that answers nothing at all is the wedged case the VBUS
 * recovery exists for. */
static bool poll_values(ups_data_t *d)
{
    /* Static, not on the stack: 16 x 63 bytes is a fifth of ups_task's. Only
     * ups_task calls this. */
    uint8_t (*payload)[REPORT_BYTES_MAX] = s_qpay;
    int     *got = s_qgot;
    bool    any = false;

    for (size_t i = 0; i < s_poll_count; i++) {
        uint8_t want = s_poll_bytes[i];
        if (want > sizeof(payload[0])) want = sizeof(payload[0]);
        got[i] = get_feature(s_poll_rid[i], payload[i], want);
        if (got[i] > 0) any = true;
    }
    if (!any) return false;

    for (size_t v = 0; v < VALUE_COUNT; v++) {
        const hid_field_t *f = pick(s_values[v].page, s_values[v].usage,
                                    s_values[v].collection);
        if (!f) continue;
        for (size_t i = 0; i < s_poll_count; i++) {
            if (s_poll_rid[i] != f->report_id || !field_fits(f, got[i])) continue;
            *(float *)((char *)d + s_values[v].offset) =
                hid_extract(f, payload[i], (size_t)got[i]);
            break;
        }
    }

    uint32_t status = 0;
    bool saw_flag = false;
    for (size_t k = 0; k < FLAG_COUNT; k++) {
        const hid_field_t *f = pick(s_flags[k].page, s_flags[k].usage,
                                    HID_COLL_NONE);
        if (!f) continue;
        for (size_t i = 0; i < s_poll_count; i++) {
            if (s_poll_rid[i] != f->report_id || !field_fits(f, got[i])) continue;
            bool on = hid_extract(f, payload[i], (size_t)got[i]) != 0.0f;
            if (s_flags[k].invert) on = !on;
            if (on) status |= s_flags[k].bit;
            saw_flag = true;
            break;
        }
    }
    /* status_hold() itself never gives up: ups_task forces a stuck hold
     * through, with a VBUS recovery, once STATUS_HOLD_US has passed (see
     * the check after this poll's result is applied). */
    if (saw_flag) {
        d->status = status_hold(status, d->status, &d->status_hold_since_us,
                                esp_timer_get_time());
    }

    if (s_date_field) {
        for (size_t i = 0; i < s_poll_count; i++) {
            if (s_poll_rid[i] != s_date_field->report_id ||
                !field_fits(s_date_field, got[i])) continue;
            decode_mfr_date((uint32_t)hid_extract(s_date_field, payload[i], (size_t)got[i]),
                            d->battery_mfr_date, sizeof(d->battery_mfr_date));
            break;
        }
    }

    for (size_t c = 0; c < CTRL_COUNT; c++) {
        const hid_field_t *f = s_ctrl_field[c];
        if (!f) continue;
        for (size_t i = 0; i < s_poll_count; i++) {
            if (s_poll_rid[i] != f->report_id || !field_fits(f, got[i])) continue;
            float v = hid_extract(f, payload[i], (size_t)got[i]);
            switch (s_ctrls[c].cap) {
            case UPS_CAP_TEST:    d->test_result   = (uint8_t)v; break;
            case UPS_CAP_BEEPER:  d->beeper        = (uint8_t)v; break;
            case UPS_CAP_LOWBATT: d->lowbatt_limit = v;          break;
            default: break;   /* the shutdown timer is not worth showing */
            }
            break;
        }
    }

    return true;
}

/* One line describing what the UPS is actually saying.
 *
 * Logged when a reading changes and as a heartbeat otherwise, rather than on
 * every poll: at a 2s interval a per-poll line is 43,000 lines a day of mostly
 * nothing, and the one line that mattered is the one nobody scrolled back far
 * enough to find. Absent values print as "-" -- a UPS not reporting a usage is
 * normal, and printing 0 for it would be a lie. */
static void log_readings(const ups_data_t *d)
{
    static ups_data_t prev;
    static int64_t    last_us;
    static bool       first = true;

    bool changed = first ||
        d->status != prev.status ||
        fabsf(d->battery_charge  - prev.battery_charge)  >= 1.0f ||
        fabsf(d->battery_runtime - prev.battery_runtime) >= 60.0f ||
        /* 3V: measured mains wanders 120<->121 all day and at 1V that logged
         * on nearly every poll. A transfer to battery shows up in the status
         * bits, which always log, so nothing important is lost by being deaf
         * to normal supply wander. */
        fabsf(d->input_voltage   - prev.input_voltage)   >= 3.0f ||
        /* 0.5V, not 0.1: a float charger ripples ~0.3V and at 0.1 this logged
         * on every single poll -- the exact spam this function exists to
         * avoid. A discharging battery moves far more than 0.5V. */
        fabsf(d->battery_voltage - prev.battery_voltage) >= 0.5f ||
        fabsf(d->ups_load        - prev.ups_load)        >= 1.0f;

    int64_t now = esp_timer_get_time();
    if (!changed && now - last_us < 30 * 1000000LL) return;
    first = false;
    prev = *d;
    last_us = now;

    char st[48];
    int o = 0;
    #define FLAG(bit, name) \
        if (d->status & (bit)) o += snprintf(st + o, sizeof(st) - o, \
                                             "%s" name, o ? "," : "")
    FLAG(UPS_STATUS_ONLINE,       "OL");
    FLAG(UPS_STATUS_ONBATT,       "OB");
    FLAG(UPS_STATUS_LOWBATT,      "LB");
    FLAG(UPS_STATUS_CHARGING,     "CHRG");
    FLAG(UPS_STATUS_DISCHARGE,    "DISCHRG");
    FLAG(UPS_STATUS_REPLACEBATT,  "RB");
    FLAG(UPS_STATUS_OVERLOAD,     "OVER");
    #undef FLAG
    if (!o) snprintf(st, sizeof(st), "(none)");

    bool est = false;
    float w = ups_power_watts(d, &est);

    char chg[12], rt[12], iv[12], bv[12], ld[12], pw[16];
    #define FMT(buf, val, spec) \
        do { if (ups_valid(val)) snprintf(buf, sizeof(buf), spec, (double)(val)); \
             else snprintf(buf, sizeof(buf), "-"); } while (0)
    FMT(chg, d->battery_charge,  "%.0f%%");
    FMT(rt,  d->battery_runtime, "%.0fs");
    FMT(iv,  d->input_voltage,   "%.1fV");
    FMT(bv,  d->battery_voltage, "%.2fV");
    FMT(ld,  d->ups_load,        "%.0f%%");
    #undef FMT
    if (ups_valid(w)) snprintf(pw, sizeof(pw), "%.0fW%s", (double)w, est ? "~" : "");
    else              snprintf(pw, sizeof(pw), "-");

    ESP_LOGI(TAG, "batt %s %s %s | in %s | load %s %s | %s",
             chg, rt, bv, iv, ld, pw, st);
}

static void ups_task(void *arg)
{
    /* Enumeration is deferred until here so the UPS gets a cold start with a
     * driver already listening. On boards without a load switch this is a
     * no-op and the UPS is powered however the board wires VBUS. */
    board_vbus_set(true);
    vTaskDelay(pdMS_TO_TICKS(500));   /* let VBUS settle before enumerating */

    int64_t next_poll_us = 0;

    for (;;) {
        /* Drives client_event_cb; must be called continuously. */
        usb_host_client_handle_events(s_client,
                                      pdMS_TO_TICKS(USB_CLIENT_EVENT_TIMEOUT_MS));

        cmd_req_t req;
        while (s_cmd_q && xQueueReceive(s_cmd_q, &req, 0) == pdTRUE) {
            esp_err_t res = req.quiet   ? set_quiet(req.quiet_on)
                          : s_quiet     ? ESP_ERR_INVALID_STATE
                          : req.recover ? do_recover()
                          : s_dev       ? execute_cmd(&req)
                                        : ESP_ERR_INVALID_STATE;
            /* A UPS's report cache has been seen to wedge during a test (an
             * APC RS 1000G reported "on mains, 100%" for 15 minutes of a real
             * outage mid-deep-test, 2026-09-27). VBUS only powers the UPS's
             * USB interface chip, not the test itself, which its own
             * controller runs regardless -- cycling it does not interrupt
             * the test, only the USB link, forcing a fresh read after the
             * one command already known to correlate with a stale one. The
             * caller still gets the test-start result in res; do_recover()'s
             * own outcome is a bonus, not something it asked about. */
            if (res == ESP_OK && !req.recover &&
                (req.cmd == UPS_CMD_TEST_QUICK || req.cmd == UPS_CMD_TEST_DEEP)) {
                do_recover();
            }
            xQueueSend(s_cmd_done, &res, 0);
        }

        /* Teardown for a device that vanished, done here rather than in the
         * event callback so nothing is freed underneath an in-flight transfer.
         * Ordered before the attach check so an unplug/replug faster than one
         * loop iteration still tears down before it builds up. */
        if (s_dev_gone) {
            /* A device that left completes whatever it had in flight; if a
             * parked transfer has not come back yet, try again next loop. */
            if (s_dev && !dev_close_safely()) continue;
            s_dev_gone = false;
            if (s_dev) {
                s_dev = NULL;
                s_hid_iface = 0xFF;
            }
            s_enum_retry = false;           /* nothing left to retry */
            s_enum_stuck = false;
            s_legacy = false;
            xSemaphoreTake(s_lock, portMAX_DELAY);
            ups_data_reset(&s_data);
            xSemaphoreGive(s_lock);
            /* The map and everything derived from it, for the same reason as
             * do_recover(): the next device may have a different descriptor. */
            memset(&s_map, 0, sizeof(s_map));
            s_poll_count = 0;
            s_date_field = NULL;
            vars_clear();                   /* slots point into s_map */
        }

        if (!s_dev && !s_quiet && (s_dev_pending ||
                       (s_enum_retry && esp_timer_get_time() >= s_enum_retry_at_us))) {
            s_dev_pending = false;
            s_enum_retry = false;
            if (!enumerate()) {
                /* Enumeration talks on the control pipe too: close only once
                 * nothing is in flight. If something is, the device stays
                 * open and counts as failing polls (s_enum_stuck), so the
                 * recovery cycle takes it from there. */
                if (s_dev && dev_close_safely()) {
                    s_dev = NULL;
                    s_hid_iface = 0xFF;
                }
                s_legacy = false;
                if (s_dev) {
                    s_enum_stuck = true;
                } else if (!s_enum_final) {
                    ESP_LOGW(TAG, "enumeration failed; trying again in %llds",
                             (long long)(s_enum_backoff_us / 1000000));
                    s_enum_retry = true;
                    s_enum_retry_at_us = esp_timer_get_time() + s_enum_backoff_us;
                    s_enum_backoff_us *= 2;
                    if (s_enum_backoff_us > ENUM_RETRY_MAX_US) s_enum_backoff_us = ENUM_RETRY_MAX_US;
                }
            } else {
                s_enum_backoff_us = ENUM_RETRY_MIN_US;
                if (s_guard_level == USB_GUARD_NORMAL) ipipe_start();
            }
        }

        /* The interrupt pipe: what arrived, then listen again. */
        if (s_ipipe_ready) {
            s_ipipe_ready = false;
            ipipe_process(s_ipipe_buf, s_ipipe_len);
        }
        ipipe_kick();

        int64_t now = esp_timer_get_time();
        if (now < next_poll_us) continue;
        next_poll_us = now + (int64_t)POLL_INTERVAL_MS * 1000;

        bool ok = false;
        bool do_vars = false;       /* a good poll: read some table variables too */
        /* An EMPTY PORT is not a failing UPS, and the difference decides
         * whether the recovery machinery below runs at all.
         *
         * Without this the counter climbed on every poll with nothing plugged
         * in, crossed FAILURES_BEFORE_RESET within seconds, and left the
         * device permanently "recovering": on the devkit an error logged
         * forever, and on Rev A a load switch cycling VBUS on an empty
         * connector every few minutes for as long as it is powered. A board
         * with no UPS attached should sit quietly and wait for one. */
        const bool have_dev = (s_dev != NULL);
        /* A UPS survived its first USB_GUARD_LIVE_US: stop charging crashes
         * to it. */
        if (s_guard.live && s_live_until_us && esp_timer_get_time() > s_live_until_us) {
            s_guard.live = 0;
            s_live_until_us = 0;
        }
        /* Nothing planned to read, or the guard says hands off: idle, not
         * failing. Counting it as a failure power-cycled VBUS on a UPS that
         * had simply answered nothing we map, on a backoff, forever. */
        const bool pollable = have_dev && (s_poll_count || s_legacy || s_enum_stuck) &&
                              s_guard_level == USB_GUARD_NORMAL && !s_quiet;

        ups_data_t fresh;
        float prev_runtime = UPS_VALUE_ABSENT;
        if (pollable) {
            xSemaphoreTake(s_lock, portMAX_DELAY);
            fresh = s_data;                 /* keep identity and link state */
            xSemaphoreGive(s_lock);
            prev_runtime = fresh.battery_runtime;
            ok = s_enum_stuck ? false
               : s_legacy     ? tl_poll(&fresh) : poll_values(&fresh);
        }

        xSemaphoreTake(s_lock, portMAX_DELAY);
        if (!have_dev) {
            /* Nothing to talk to. Hold the counters at rest so an empty port
             * accumulates no fault and the recovery below stays idle; the
             * disconnect teardown has already invalidated the readings. */
            s_data.poll_failures = 0;
        } else if (!pollable) {
            s_data.poll_failures = 0;       /* attached, identity kept */
        } else if (ok) {
            /* Copy readings back; identity and counters stay authoritative
             * here, not in the snapshot the poll worked on. */
            fresh.attached       = true;
            fresh.poll_failures  = 0;
            fresh.last_update_us = esp_timer_get_time();
            if (fresh.battery_runtime != UPS_VALUE_ABSENT &&
                (fresh.runtime_changed_us == 0 ||
                 fabsf(fresh.battery_runtime - prev_runtime) >= 1.0f)) {
                fresh.runtime_changed_us = fresh.last_update_us;
            }
            s_data = fresh;
            log_readings(&fresh);
            do_vars = true;
        } else {
            s_data.poll_failures++;
            if (s_data.poll_failures >= FAILURES_BEFORE_RESET) {
                if (s_data.attached) {
                    ESP_LOGW(TAG, "%u consecutive poll failures, dropping the "
                                  "readings rather than serving stale ones",
                             (unsigned)s_data.poll_failures);
                }
                s_data.attached = false;
                invalidate_readings(&s_data);
                /* NUT's status and table values too. They are rebuilt by the
                 * next good poll; left alone they kept NUT answering "OL"
                 * for a UPS that had stopped talking, through a power cut. */
                s_nst_valid = false;
                for (size_t k = 0; k < s_var_count; k++) s_vars[k].valid = false;
                s_mb_nvars = 0;
                s_mbs.live = false;         /* read the nameplate again */
            }
        }
        uint32_t failures = s_data.poll_failures;
        xSemaphoreGive(s_lock);
        if (do_vars) {                      /* each takes s_lock itself */
            poll_status(s_data.battery_charge);
            poll_vars();
            mb_poll();
        }

        if (ok || !pollable) {
            /* A good poll, or nothing to poll: either way the next UPS to
             * misbehave starts from a fresh backoff rather than inheriting
             * one from a device that is no longer there. */
            s_recovery_backoff_us = RECOVERY_BACKOFF_MIN_US;
            s_next_recovery_us = 0;
        } else if (failures >= FAILURES_BEFORE_RESET) {
            int64_t t = esp_timer_get_time();
            if (t >= s_next_recovery_us) {
                ESP_LOGW(TAG, "UPS unresponsive, attempting recovery "
                              "(next attempt in %llds)",
                         (long long)(s_recovery_backoff_us / 1000000));
                /* Directly, not ups_hid_recover(): this IS ups_task, and the
                 * public entry point queues work for this task to do. Calling
                 * it here would block waiting for a queue only this task
                 * drains. */
                do_recover();
                s_next_recovery_us = t + s_recovery_backoff_us;
                s_recovery_backoff_us *= 2;
                if (s_recovery_backoff_us > RECOVERY_BACKOFF_MAX_US) {
                    s_recovery_backoff_us = RECOVERY_BACKOFF_MAX_US;
                }
            }
        }

        /* The poll itself succeeded -- this is not the unresponsive case
         * above -- but the status has read all-zero, held rather than
         * reported, for longer than a post-test glitch should ever run.
         * Force it through with the same VBUS recovery used for a wedged
         * link, on the chance a fresh enumeration clears whatever cached the
         * stale report. */
        if (ok && fresh.status_hold_since_us != 0 &&
            now - fresh.status_hold_since_us >= STATUS_HOLD_US) {
            ESP_LOGW(TAG, "UPS status has read all-zero for over %llds "
                          "despite good polls, forcing a VBUS recovery",
                     (long long)(STATUS_HOLD_US / 1000000));
            do_recover();
        }
    }
}

esp_err_t ups_hid_start(void)
{
    /* Data first, lock second: ups_hid_get() treats a NULL lock as "not
     * started", so once the lock exists the data behind it must be valid. */
    ups_data_reset(&s_data);
    s_lock = xSemaphoreCreateMutex();
    if (!s_lock) return ESP_ERR_NO_MEM;
    memset(&s_map, 0, sizeof(s_map));
    /* Vendor-page usages NUT's tables read: kept by the parser, the rest of
     * a vendor page dropped. */
    hid_parser_keep_vendor(ups_vartab_vendor_usages, ups_vartab_vendor_usage_count);

    s_ctrl_done = xSemaphoreCreateBinary();
    if (!s_ctrl_done) return ESP_ERR_NO_MEM;

    s_cmd_q    = xQueueCreate(4, sizeof(cmd_req_t));
    s_cmd_done = xQueueCreate(1, sizeof(esp_err_t));
    if (!s_cmd_q || !s_cmd_done) return ESP_ERR_NO_MEM;

    esp_reset_reason_t rr = esp_reset_reason();
    bool crashed = rr == ESP_RST_PANIC || rr == ESP_RST_INT_WDT ||
                   rr == ESP_RST_TASK_WDT || rr == ESP_RST_WDT;
    s_guard_level = usb_guard_boot(&s_guard, crashed);
    if (s_guard_level == USB_GUARD_USB_OFF) {
        board_vbus_set(false);
        ESP_LOGE(TAG, "the UPS crashed this board %u times in a row: USB is OFF "
                      "until a clean restart", s_guard.crashes);
        return ESP_OK;              /* no USB host; the rest of the board runs */
    }
    if (s_guard_level == USB_GUARD_NO_POLL) {
        ESP_LOGE(TAG, "the UPS crashed this board %u times in a row: reading its "
                      "name and descriptor only, not polling it", s_guard.crashes);
    }

    const usb_host_config_t host_cfg = {
        .skip_phy_setup = false,
        .intr_flags = ESP_INTR_FLAG_LEVEL1,
    };
    esp_err_t err = usb_host_install(&host_cfg);
    if (err != ESP_OK) {
        ESP_LOGE(TAG, "usb_host_install failed: %s", esp_err_to_name(err));
        return err;
    }

    /* Measured deepest ~1 KB (v0.08, memdiag, a UPS attached and polled):
     * it only pumps usb_host_lib_handle_events. */
    if (xTaskCreate(usb_lib_task, "usb_lib", 3072, NULL, 6, NULL) != pdPASS) {
        return ESP_ERR_NO_MEM;
    }

    const usb_host_client_config_t client_cfg = {
        .is_synchronous = false,
        .max_num_event_msg = 8,
        .async = {
            .client_event_callback = client_event_cb,
            .callback_arg = NULL,
        },
    };
    err = usb_host_client_register(&client_cfg, &s_client);
    if (err != ESP_OK) {
        ESP_LOGE(TAG, "client_register failed: %s", esp_err_to_name(err));
        return err;
    }

    if (xTaskCreate(ups_task, "ups_hid", 5120, NULL, 5, NULL) != pdPASS) {
        return ESP_ERR_NO_MEM;
    }
    ESP_LOGI(TAG, "USB host started, waiting for a UPS");
    return ESP_OK;
}

void ups_hid_get(ups_data_t *out)
{
    /* Callers start before this component does -- the web UI and the display
     * both come up ahead of ups_hid_start() in app_main, and the display's
     * first refresh used to take a lock that did not exist yet and abort.
     * Before start there is no UPS and nothing measured, so say exactly that. */
    if (!s_lock) {
        ups_data_reset(out);
        return;
    }
    xSemaphoreTake(s_lock, portMAX_DELAY);
    memcpy(out, &s_data, sizeof(*out));
    xSemaphoreGive(s_lock);
}

/* Commands run on the polling task, never on the caller's.
 *
 * ctrl_in and ctrl_out both pump usb_host_client_handle_events, and that pump
 * belongs to one task. A command arriving from the web server's task would be
 * a second pumper on the same client -- so requests are queued, the poll loop
 * executes them between polls, and the caller waits for the result. */
static uint32_t cap_for_cmd(ups_cmd_t c)
{
    switch (c) {
    case UPS_CMD_TEST_QUICK:
    case UPS_CMD_TEST_DEEP:
    case UPS_CMD_TEST_ABORT:      return UPS_CAP_TEST;
    case UPS_CMD_BEEPER_DISABLE:
    case UPS_CMD_BEEPER_ENABLE:
    case UPS_CMD_BEEPER_MUTE:     return UPS_CAP_BEEPER;
    case UPS_CMD_LOWBATT_LIMIT:   return UPS_CAP_LOWBATT;
    case UPS_CMD_LOAD_OFF:        return UPS_CAP_SHUTDOWN;
    case UPS_CMD_BATTERY_DATE:    return UPS_CAP_BATTDATE;
    }
    return 0;
}

static esp_err_t execute_cmd(const cmd_req_t *r)
{
    uint32_t cap = cap_for_cmd(r->cmd);
    const hid_field_t *f = (cap == UPS_CAP_BATTDATE) ? s_date_field : ctrl_for(cap);
    if (!f) return ESP_ERR_NOT_SUPPORTED;

    uint32_t v;
    switch (r->cmd) {
    case UPS_CMD_TEST_QUICK:      v = UPS_TEST_CMD_QUICK;      break;
    case UPS_CMD_TEST_DEEP:       v = UPS_TEST_CMD_DEEP;       break;
    case UPS_CMD_TEST_ABORT:      v = UPS_TEST_CMD_ABORT;      break;
    case UPS_CMD_BEEPER_DISABLE:  v = UPS_BEEPER_DISABLED; break;
    case UPS_CMD_BEEPER_ENABLE:   v = UPS_BEEPER_ENABLED;  break;
    case UPS_CMD_BEEPER_MUTE:     v = UPS_BEEPER_MUTED;    break;
    case UPS_CMD_BATTERY_DATE: {
        /* A packed date, not a quantity: no physical range applies. */
        int32_t hi = (f->bit_size >= 32) ? INT32_MAX : (int32_t)((1u << f->bit_size) - 1);
        if (r->arg < 0)  return ESP_ERR_INVALID_ARG;
        v = (uint32_t)(r->arg > hi ? hi : r->arg);
        break;
    }
    case UPS_CMD_LOWBATT_LIMIT:
    case UPS_CMD_LOAD_OFF: {
        /* The argument is physical (percent, seconds); the UPS may count in
         * something else. Every CyberPower captured declares its shutdown
         * delay in minutes logically and seconds physically, and this used to
         * write the seconds raw: the page's "60 seconds first" meant an HOUR.
         * A delay rounds UP, never sooner than asked. Too big for the field
         * clamps to the field's maximum: later, the safe direction for a
         * shutdown timer, rather than wrapping into something sooner. */
        if (r->arg < 0) return ESP_ERR_INVALID_ARG;
        bool up = (r->cmd == UPS_CMD_LOAD_OFF);
        if (!hid_to_raw(f, (double)r->arg, up, &v)) {
            v = (f->bit_size >= 32) ? UINT32_MAX : (uint32_t)((1ull << f->bit_size) - 1);
            if (f->is_signed) v >>= 1;          /* largest positive value */
        }
        if (f->has_phys) {
            ESP_LOGI(TAG, "command %d: %ld physical -> %lu raw (x%.3g%+.3g)",
                     (int)r->cmd, (long)r->arg, (unsigned long)v,
                     (double)f->phys_scale, (double)f->phys_offset);
        }
        break;
    }
    default: return ESP_ERR_INVALID_ARG;
    }

    ESP_LOGI(TAG, "command %d -> report %u = %lu",
             (int)r->cmd, f->report_id, (unsigned long)v);
    return set_field(f, v) ? ESP_OK : ESP_FAIL;
}

/* Is this argument meaningful, as opposed to merely representable?
 *
 * execute_cmd() already clamps to the width of the descriptor's field, which
 * stops a value wrapping into a different meaning. That is not the same check:
 * a field being wide enough to hold 255 does not make 255 a battery
 * percentage. Both commands that take a human-meaningful argument are
 * reachable without authentication -- the NUT server accepts
 * SET VAR battery.charge.low from any client on 3493 -- and that variable is
 * what decides when the UPS tells the machines it protects to shut down.
 * Setting it to 0 means it may never warn them; clamping 9999 to 255 means it
 * warns immediately and forever.
 *
 * The date rules deliberately mirror decode_mfr_date(), so a value this
 * accepts is one the firmware can read back. */
static bool arg_is_sane(ups_cmd_t cmd, int32_t arg)
{
    switch (cmd) {
    case UPS_CMD_LOWBATT_LIMIT:
        return arg >= 0 && arg <= 100;              /* a percentage */
    case UPS_CMD_LOAD_OFF:
        return arg >= 0;                            /* seconds of delay */
    case UPS_CMD_BATTERY_DATE: {
        if (arg <= 0 || arg > 0xFFFF) return false; /* the field is 16 bits */
        unsigned day = (unsigned)arg & 0x1F;
        unsigned mon = ((unsigned)arg >> 5) & 0x0F;
        unsigned yr  = 1980 + ((unsigned)arg >> 9);
        return day >= 1 && day <= 31 && mon >= 1 && mon <= 12 && yr <= 2107;
    }
    default:
        return true;                                /* takes no argument */
    }
}

esp_err_t ups_hid_command(ups_cmd_t cmd, int32_t arg)
{
    if (!s_cmd_q) return ESP_ERR_INVALID_STATE;
    if (!arg_is_sane(cmd, arg)) return ESP_ERR_INVALID_ARG;

    xSemaphoreTake(s_lock, portMAX_DELAY);
    bool attached = s_data.attached;
    uint32_t caps = s_data.caps;
    xSemaphoreGive(s_lock);

    if (!attached) return ESP_ERR_INVALID_STATE;
    if (!(caps & cap_for_cmd(cmd))) return ESP_ERR_NOT_SUPPORTED;

    cmd_req_t r = { .cmd = cmd, .arg = arg };
    xQueueReset(s_cmd_done);
    if (xQueueSend(s_cmd_q, &r, pdMS_TO_TICKS(100)) != pdTRUE) return ESP_ERR_TIMEOUT;

    esp_err_t res = ESP_ERR_TIMEOUT;
    xQueueReceive(s_cmd_done, &res, pdMS_TO_TICKS(5000));
    return res;
}

size_t ups_hid_report_descriptor(const uint8_t **out)
{
    if (!s_dev || !s_report_desc_len) return 0;
    if (out) *out = s_report_desc;
    return s_report_desc_len;
}

/* The recovery itself. ONLY ever runs in ups_task, which is what makes the
 * unlocked writes below safe: s_map, the poll plan and s_date_field are owned
 * by that task and touched nowhere else.
 *
 * It did not used to be. ups_hid_recover() ran this in the CALLER's task --
 * the web server, for the "reset UPS link" button -- and on Rev A that is a
 * two-second blocking VBUS cycle (CONFIG_UPSA_VBUS_CYCLE_MS) during which
 * ups_task keeps running: the UPS disconnects, VBUS returns, and the device
 * can re-enumerate and repopulate s_map before the web server task reaches the
 * memset. Clearing it then wipes a map the poll plan is already pointing into,
 * and the UPS sits there attached and permanently unreadable until someone
 * unplugs it by hand -- a recovery that causes the fault it exists to clear.
 *
 * Invisible on the Freenove devkit, which has no load switch: board_vbus_cycle()
 * returns ESP_ERR_NOT_SUPPORTED immediately, so there is no window and no
 * re-enumeration. This is a Rev A-only defect found by reading, not running. */
static esp_err_t do_recover(void)
{
    esp_err_t err = board_vbus_cycle();

    /* Pump events briefly so a disconnect caused by the cycle lands now, and
     * the loop's DEV_GONE teardown -- not the code below -- owns that case. */
    int64_t until = esp_timer_get_time() + (int64_t)VBUS_GONE_WAIT_MS * 1000;
    while (!s_dev_gone && esp_timer_get_time() < until) {
        usb_host_client_handle_events(s_client, pdMS_TO_TICKS(100));
    }

    /* A SELF-POWERED UPS DOES NOT LEAVE. Its USB interface runs from its own
     * supply, so dropping VBUS does not disconnect it: no DEV_GONE, no
     * NEW_DEV. The map was then wiped below and nothing ever rebuilt it,
     * because only enumeration does -- the UPS stayed attached and was never
     * polled again, until someone replugged it by hand. The first Rev A board
     * did this to an APC Back-UPS RS 1000G on 2026-09-25, from both the
     * page's button and the automatic recovery; the devkit has no load switch
     * and could never have shown it.
     *
     * So if it is still here, close it and enumerate it again at the same
     * address: a fresh descriptor read, the map rebuilt, and whatever state
     * the interface was wedged in is at least re-requested from scratch. */
    if (s_dev && !s_dev_gone) {
        ESP_LOGW(TAG, "UPS stayed connected through the VBUS cycle "
                      "(self-powered), re-enumerating it in place");
        if (!dev_close_safely()) {
            /* Next recovery retries. Until then nothing read from this UPS
             * may be served as current: NUT kept answering its last "OL"
             * through this, so a power cut meanwhile was never reported. */
            xSemaphoreTake(s_lock, portMAX_DELAY);
            s_data.attached = false;
            invalidate_readings(&s_data);
            s_nst_valid = false;
            for (size_t k = 0; k < s_var_count; k++) s_vars[k].valid = false;
            s_mb_nvars = 0;
            xSemaphoreGive(s_lock);
            s_mbs.live = false;
            return ESP_ERR_INVALID_STATE;
        }
        s_dev = NULL;
        s_hid_iface = 0xFF;
        s_legacy = false;
        s_enum_stuck = false;
        s_enum_retry = false;
        s_dev_pending = true;          /* s_dev_addr is unchanged */
    }

    xSemaphoreTake(s_lock, portMAX_DELAY);
    ups_data_reset(&s_data);          /* descriptor may differ after re-enum */
    xSemaphoreGive(s_lock);

    /* The map and everything derived from it go together. s_poll_rid/_bytes
     * and s_date_field are indexes and pointers INTO s_map, so clearing the
     * map alone leaves the poll loop reading a zeroed descriptor through a
     * plan that still looks valid. */
    memset(&s_map, 0, sizeof(s_map));
    s_poll_count = 0;
    s_date_field = NULL;
    vars_clear();                           /* slots point into s_map */

    return err;
}

esp_err_t ups_hid_recover(void)
{
    if (!s_cmd_q) return ESP_ERR_INVALID_STATE;
    /* No ups_task to hand it to: USB was never started this boot. */
    if (s_guard_level == USB_GUARD_USB_OFF) return ESP_ERR_INVALID_STATE;

    /* Hand it to ups_task and wait for the answer, so the map is only ever
     * written by its owner. The timeout allows for the VBUS off-time plus
     * whatever transfer the task has to finish before it picks this up. */
    cmd_req_t r = { .recover = true };
    xQueueReset(s_cmd_done);
    if (xQueueSend(s_cmd_q, &r, pdMS_TO_TICKS(100)) != pdTRUE) return ESP_ERR_TIMEOUT;

    esp_err_t res = ESP_ERR_TIMEOUT;
    xQueueReceive(s_cmd_done, &res,
                  pdMS_TO_TICKS(CONFIG_UPSA_VBUS_CYCLE_MS + 8000));
    return res;
}

esp_err_t ups_hid_quiet(bool quiet)
{
    if (!s_cmd_q) return ESP_ERR_INVALID_STATE;
    if (s_guard_level == USB_GUARD_USB_OFF) return ESP_OK;   /* already silent */

    cmd_req_t r = { .quiet = true, .quiet_on = quiet };
    xQueueReset(s_cmd_done);
    if (xQueueSend(s_cmd_q, &r, pdMS_TO_TICKS(1000)) != pdTRUE) return ESP_ERR_TIMEOUT;

    /* Long enough for a poll in progress to finish, plus ipipe_stop()'s own
     * wait for a cancelled transfer to come back. */
    esp_err_t res = ESP_ERR_TIMEOUT;
    xQueueReceive(s_cmd_done, &res, pdMS_TO_TICKS(8000));
    return res;
}

int ups_hid_guard_level(void)
{
    return (int)s_guard_level;
}
