aronreid/ups-to-esp32/firmware/components/ups_hid/include/apc_modbus.h

/* SPDX-License-Identifier: GPL-3.0-or-later
 *
 * APC Modbus over USB: the readings an APC Smart-UPS keeps out of its HID
 * interface.
 *
 * Some Smart-UPS units on 051d:0003 (a Smart-UPS C 1500 on firmware UPS 15.1
 * among them) report only charge, runtime and status over HID. Their input
 * and output voltage, load, current and frequency are available only through
 * APC's Modbus register map. NUT reads that with its apc_modbus driver, and on
 * USB the transport is a pair of vendor reports on the same HID interface:
 * usage page 0xFF86, usage 0xFC for an Output report carrying a request to the
 * UPS, usage 0xFD for an Input report carrying its reply. Each report is the
 * report ID and 63 bytes of Modbus RTU frame, zero-padded, with no CRC (USB
 * already checks the bytes). A reply longer than 63 bytes continues in the
 * next report.
 *
 * The UPS answers only with Modbus turned on in its front-panel menu
 * (Configuration, Modbus, Enable). The vendor reports are in the descriptor
 * either way, so their presence says what to try, not that it will work.
 *
 * This is the protocol half: finding the reports, building a request,
 * reassembling a reply and decoding registers. Nothing touches USB, so
 * tools/test/test_apc_modbus.py compiles and runs it on the host. The
 * transport is in ups_hid.c.
 *
 * The register map and scaling are NUT's drivers/apc_modbus.c (GPL-2.0-or-
 * later, Copyright (C) 2023 Axel Gembe <axel@gembe.net>), and the USB framing
 * is the rtu_usb backend of the libmodbus fork it builds against (LGPL-2.1-or-
 * later, same author).
 */
#ifndef UPSA_APC_MODBUS_H
#define UPSA_APC_MODBUS_H

#include <stdbool.h>
#include <stddef.h>
#include <stdint.h>

#define APCMB_VID           0x051D
#define APCMB_REPORT        64      /* report ID + 63 bytes of frame */
#define APCMB_PAYLOAD       63
#define APCMB_SLAVE         1       /* NUT's default slave id */
#define APCMB_MAX_REGS      64

/* Blocks this firmware reads, from NUT's register maps. */
#define APCMB_NOM_ADDR      588     /* ups.power.nominal, ups.realpower.nominal */
#define APCMB_NOM_COUNT     2
#define APCMB_DYN_ADDR      128     /* NUT's "dynamic" block: 128..171 */
#define APCMB_DYN_COUNT     44

/* The two vendor report IDs in a report descriptor: `to_ups` carries a
 * request (Output, usage 0xFF86:0xFC), `from_ups` a reply (Input, usage
 * 0xFF86:0xFD). False unless both are there. */
bool apcmb_find_reports(const uint8_t *desc, size_t len, uint8_t *to_ups, uint8_t *from_ups);

/* A Read Holding Registers (function 3) request for `count` registers from
 * `addr`, as one wire report. */
void apcmb_build_read(uint8_t report_id, uint8_t slave, uint16_t addr, uint16_t count,
                      uint8_t out[APCMB_REPORT]);

/* A reply being reassembled from reports. */
typedef struct {
    uint8_t  slave;
    uint16_t count;                 /* registers asked for */
    uint8_t  frame[3 + 2 * APCMB_MAX_REGS];
    size_t   len;
    uint8_t  exception;             /* the code, after APCMB_EXCEPTION */
} apcmb_rx_t;

typedef enum {
    APCMB_MORE = 0,     /* the frame continues in the next report */
    APCMB_DONE,         /* regs[] holds the registers */
    APCMB_EXCEPTION,    /* the UPS refused the read: rx->exception */
    APCMB_FOREIGN,      /* not a reply to this request (a late one to an
                         * earlier request, say): dropped, keep waiting */
} apcmb_rx_status_t;

void apcmb_rx_init(apcmb_rx_t *rx, uint8_t slave, uint16_t count);

/* One reply report's 63 bytes, the report ID already stripped. */
apcmb_rx_status_t apcmb_rx_feed(apcmb_rx_t *rx, const uint8_t *payload, size_t n,
                                uint16_t *regs);

/* The values NUT's apc_modbus publishes from the two blocks above. NAN-free:
 * APCMB_ABSENT where there is no value. */
#define APCMB_ABSENT (-1e30)
typedef struct {
    double power_nominal;           /* VA */
    double realpower_nominal;       /* W */
    double battery_voltage;
    double battery_temperature;
    double load;                    /* % */
    double realpower;               /* W, load x realpower_nominal */
    double power;                   /* VA */
    double output_current;
    double output_voltage;
    double output_frequency;
    double input_voltage;
    double efficiency;              /* %, or APCMB_ABSENT with efficiency_word */
    const char *efficiency_word;    /* "OnBattery" etc., NULL for a number */
} apcmb_reading_t;

void apcmb_reading_init(apcmb_reading_t *r);
void apcmb_decode_nominal(const uint16_t regs[APCMB_NOM_COUNT], apcmb_reading_t *r);
void apcmb_decode_dynamic(const uint16_t regs[APCMB_DYN_COUNT], apcmb_reading_t *r);

/* A reading as NUT variables: name and value text, in NUT's formats. */
typedef struct { const char *name; char value[24]; } apcmb_var_t;
#define APCMB_MAX_VARS 13
size_t apcmb_vars(const apcmb_reading_t *r, apcmb_var_t out[APCMB_MAX_VARS]);

/* When to talk to the UPS, as a state machine the host tests can drive.
 *
 * A Smart-UPS with Modbus switched off never answers, and must cost one short
 * stall every few minutes rather than every poll. One that stops answering
 * keeps its readings for a couple of polls (a glitch), then loses them rather
 * than serving stale numbers, and is asked again a minute later. A read that
 * gave way to a waiting command (APCMB_R_YIELD) counts for nothing. */
#define APCMB_RETRY_US       (5LL * 60 * 1000000)  /* after no answer at all */
#define APCMB_LOST_RETRY_US  (60LL * 1000000)      /* after it stopped answering */
#define APCMB_FAILS_TO_DROP  3                     /* failed reads in a row */

typedef struct {
    bool    live;           /* answering: the nameplate is read */
    bool    told;           /* the "turn Modbus on" hint is logged, once */
    int     fails;          /* failed reads in a row while live */
    int64_t next_us;        /* nothing before this */
} apcmb_sched_t;

typedef enum { APCMB_IDLE = 0, APCMB_PROBE, APCMB_READ } apcmb_step_t;
typedef enum { APCMB_R_OK = 0, APCMB_R_FAIL, APCMB_R_YIELD } apcmb_result_t;
#define APCMB_EV_HINT  1u   /* log the "turn Modbus on" hint */
#define APCMB_EV_UP    2u   /* it answered: read the nameplate's reply, then READ */
#define APCMB_EV_DROP  4u   /* it stopped answering: withdraw the readings */

void         apcmb_sched_init(apcmb_sched_t *s);
apcmb_step_t apcmb_sched_step(const apcmb_sched_t *s, int64_t now_us);
unsigned     apcmb_sched_done(apcmb_sched_t *s, apcmb_step_t step, apcmb_result_t r,
                              int64_t now_us);

#endif /* UPSA_APC_MODBUS_H */
